tobias-weiss-ai-xr/mykovolt/docs/technical/MykoVolt_Papers.md

# Paper Collection — Fungal Bio-Battery / Mycelium Electronics

> **Stand:** Juni 2026 | **Kuratierte Sammlung** aus den Bereichen Pilz-MFC, Myzel-Elektronik, Laccase-Bioelektrochemie, Yeast-Biofuel-Cells, MycelioTronics, AI-gestützte Forschung und Marktberichte.
>
> Alle Papers nach Relevanz und Themenclustern sortiert. DOIs und Direktlinks wo verfügbar.

---

## 1. KERN: 3D-gedruckte Pilz-Batterie (Empa)

| # | Titel | Autoren | Journal | Jahr | DOI / Link |
|---|---|---|---|---|---|
| 1 | **3D Printed Cellulose-Based Fungal Battery** | C. Reyes, E. Fivaz, Z. Sajó, A. Schneider, G. Siqueira, J. Ribera, A. Poulin, F.W.M.R. Schwarze, G. Nyström | ACS Sustainable Chemistry & Engineering | 2024 | [10.1021/acssuschemeng.4c05494](https://doi.org/10.1021/acssuschemeng.4c05494) |
| 2 | Empa Pressemitteilung: Fungal biobattery | — | empa.ch | 2025 | [empa.ch/web/s604/fungal-biobattery](https://www.empa.ch/web/s604/fungal-biobattery) |
| 3 | News: The battery that eats itself | H. Hall | R&D World | 2025 | [rdworldonline.com/...](https://www.rdworldonline.com/the-battery-that-eats-itself-fungal-power-with-a-built-in-cleanup-crew/) |
| 4 | News: Swiss scientists have taught fungi to generate electricity | — | Euronews | 2025 | [euronews.com/...](https://www.euronews.com/2025/01/11/swiss-scientists-have-taught-fungi-to-generate-electricity-how-do-mushroom-batteries-work) |
| 5 | News: 3D-printed battery made from fungi feeds on sugars | — | New Atlas | 2025 | [newatlas.com/...](https://newatlas.com/energy/3d-printed-battery-fungi-sugars-empa/) |
| 6 | News: 3D-printed fungi batteries: A path to a biodegradable tech future? | — | Anadolu Ajansı | 2025 | [aa.com.tr/...](https://www.aa.com.tr/en/science-technology/3d-printed-fungi-batteries-a-path-to-a-biodegradable-tech-future/3463854) |

**Key Facts (Reyes 2024):**
- Erstmalige Kombination von Hefe (Anode) + Weißfäulepilz (Kathode) in 3D-gedruckter MFC
- Drucktinte: Cellulose-Nanokristalle + Nanofibrillen + Carbon Black + Graphitflocken
- Leistung: 12,5 µW/cm², 300–600 mV für mehrere Tage
- 4 Zellen parallel → Sensor-Betrieb für 65 h
- Vollständig biologisch abbaubar (Cellulose-Membran, Bienenwachs-Gehäuse)

---

## 2. REVIEWS & ÜBERSICHTSARBEITEN

| # | Titel | Autoren | Journal | Jahr | DOI / Link |
|---|---|---|---|---|---|
| 7 | **Fungi-Based Microbial Fuel Cells** | A. Sekrecka-Belniak, R. Toczyłowska-Mamińska | Energies (MDPI) | 2018 | [10.3390/en11102827](https://doi.org/10.3390/en11102827) |
| 8 | **Harnessing fungal bio-electricity: a promising path to a cleaner environment** | A. Umar et al. | Frontiers in Microbiology | 2024 | [10.3389/fmicb.2023.1291904](https://www.frontiersin.org/journals/microbiology/articles/10.3389/fmicb.2023.1291904/full) |
| 9 | **Bioelectricity harvesting from microorganism: review of recent advancements in utilizing the bioelectric properties of fungi for powering small-scale robotic systems** | — | Frontiers in Fungal Biology | 2026 | [10.3389/ffunb.2025.1739847](https://www.frontiersin.org/journals/fungal-biology/articles/10.3389/ffunb.2025.1739847/full) |
| 10 | **Fungal fuel cells: an environmentally friendly approach to addressing heavy metal pollution and electricity production** | — | Frontiers in Microbiology | 2026 | [10.3389/fmicb.2026.1825368](https://www.frontiersin.org/journals/microbiology/articles/10.3389/fmicb.2026.1825368/full) |
| 11 | **The Role of Fungal Fuel Cells in Energy Production and the Removal of Pollutants from Wastewater** | — | Catalysts (MDPI) | 2023 | [10.3390/catal13040687](https://doi.org/10.3390/catal13040687) |
| 12 | **Fungal-mediated electrochemical system: Prospects, applications and challenges** | — | PMC / ScienceDirect | 2021 | [pmc.ncbi.nlm.nih.gov/articles/PMC8610361](https://pmc.ncbi.nlm.nih.gov/articles/PMC8610361/) |
| 13 | **Fungal-mediated microbial electrochemical system: Exciting development, possible application and certain challenges** | — | ResearchGate | 2021 | [researchgate.net/...](https://www.researchgate.net/publication/351976135_Fungal-mediated_microbial_electrochemical_system_Exciting_development_possible_application_and_certain_challenges) |
| 14 | **Recent trends in upgrading the performance of yeast as electrode biocatalyst in microbial fuel cells** | — | Chemosphere | 2021 | [10.1016/j.chemosphere.2021.131330](https://www.sciencedirect.com/science/article/abs/pii/S0045653521018555) |
| 15 | **Microbial Biofuel Cells: Fundamental Principles, Development and Recent Obstacles** | — | Biosensors (MDPI) | 2023 | [pmc.ncbi.nlm.nih.gov/articles/PMC9954062](https://pmc.ncbi.nlm.nih.gov/articles/PMC9954062/) |
| 16 | **New horizons in microbial fuel cell technology: applications, challenges, and prospects** | — | Biotechnol. Biofuels Bioprod. | 2025 | [10.1186/s13068-025-02649-y](https://link.springer.com/article/10.1186/s13068-025-02649-y) |
| 17 | **Harnessing the power of microbial fuel cells as pioneering green technology** | — | Bioprocess Biosyst. Eng. | 2025 | [10.1007/s00449-024-03115-z](https://link.springer.com/article/10.1007/s00449-024-03115-z) |
| 18 | **A Review of Recent Advances in Microbial Fuel Cells: Preparation, Operation, and Application** | — | BioTech (MDPI) | 2022 | [pmc.ncbi.nlm.nih.gov/articles/PMC9589990](https://pmc.ncbi.nlm.nih.gov/articles/PMC9589990/) |

---

## 3. HÖCHSTLEISTUNGSSTUDIEN

### 3.1 Phanerochaete chrysosporium (Weißfäule — 1,9 W/m²)

| # | Titel | Leistung | Journal | Jahr | DOI / Link |
|---|---|---|---|---|---|
| 19 | **Self-Sustaining Bioelectrochemical Cell from Fungal Degradation of Lignin-Rich Agrowaste** | **1,9 W/m²** (3,1 A/m²), **1056 mAh**, 44 Tage @ 1 mA, OCV 1,2 V | Energies (MDPI) | 2021 | [10.3390/en14082098](https://doi.org/10.3390/en14082098) |
| 20 | Conversion of lignocellulosic biomass: Production of bioethanol and bioelectricity using wheat straw hydrolysate | 65,09 mW/m² | Bioresour. Technol. | 2023 | [pmc.ncbi.nlm.nih.gov/articles/PMC9873701](https://pmc.ncbi.nlm.nih.gov/articles/PMC9873701/) |

**⭐ Wichtigste Einzelstudie:** Sukri et al. 2021 — mit *P. chrysosporium* wurde die höchste je gemessene Leistung einer Pilz-MFC erreicht (1,9 W/m²). Zink/Luft-Zelle, membranlos, 44 Tage stabil.

### 3.2 Trametes versicolor

| # | Titel | Leistung | Journal | Jahr | DOI / Link |
|---|---|---|---|---|---|
| 21 | A white-rot fungus is used as a biocathode to improve electricity production of an MFC | 320 ± 30 mW/m³ (laccase: 480 mW/m³) | Applied Energy | 2012 | — |
| 22 | In situ Trametes versicolor laccase biocathode performance assessment in dual-chamber MFCs | 42,8 mA/m² (2,1× Kontrolle) | Bioenergy Research | 2023 | [10.1007/s12155-023-10594-7](https://doi.org/10.1007/s12155-023-10594-7) |
| 23 | Hybrid microbial–enzymatic fuel cell cathode overcomes enzyme inactivation limits | Self-regenerierende Kathode | Catalysts (MDPI) | 2021 | [mdpi-res.com/.../catalysts-11-00242.pdf](https://mdpi-res.com/d_attachment/catalysts/catalysts-11-00242/article_deploy/catalysts-11-00242-v3.pdf) |
| 24 | Decolorization of azo dye and generation of electricity by MFC with laccase-producing white-rot fungus on cathode | 276,9 mW/m² | Applied Energy | 2017 | — |

### 3.3 Ganoderma lucidum & Ganoderma gibbosum

| # | Titel | Leistung | Journal | Jahr | DOI / Link |
|---|---|---|---|---|---|
| 25 | **Electricity generation and oxidoreductase potential during dye discoloration by laccase-producing Ganoderma gibbosum in fungal fuel cell** | 810 mV OCV, 14,18 mW/m², 35 mA/m² | Microb. Cell Fact. | 2023 | [10.1186/s12934-023-02258-0](https://microbialcellfactories.biomedcentral.com/articles/10.1186/s12934-023-02258-0) |
| 26 | Ganoderma lucidum BCRC 36123 als Biokathode | 207 mW/m² | diverse | — | — |

### 3.4 Pleurotus spp. (Austernpilze)

| # | Titel | Leistung | Journal | Jahr | DOI / Link |
|---|---|---|---|---|---|
| 27 | Improved Performance of a Novel-Model Laccase-based MFC (Pleurotus pulmonarius) | **940 mV** OCV, 13,22 mW/m², 97 mA/m² | PJOES | 2023 | [pjoes.com/pdf-147196-78069](https://www.pjoes.com/pdf-147196-78069) |
| 28 | Reducing Plastic Waste and Generating Bioelectricity Simultaneously — Pleurotus ostreatus | 86,3 mW/cm² (!), 0,427 V | Sustainability (MDPI) | 2024 | [doi.org/10.3390/su16187909](https://www.mdpi.com/2071-1050/16/18/7909) |
| 29 | MIND Device: Mycoponically Integrated Network Device — Pleurotus ostreatus | >11 Monate stabiles Myzel-Netzwerk | arXiv | 2026 | [arxiv.org/html/2604.22947](https://arxiv.org/html/2604.22947) |
| 30 | Selective natural induction of laccases in Pleurotus sajor-caju for biofuel cell cathode | −148 µA/cm² bei pH 5; −102 µA/cm² bei pH 7 | Bioresour. Technol. | 2016 | — |

### 3.5 Aspergillus, Paecilomyces, Trichoderma (Plastikabbau)

| # | Titel | Pilz | Leistung | Journal | Jahr | DOI / Link |
|---|---|---|---|---|---|---|
| 31 | Performance of the Dual-Chamber Fungal Fuel Cell in Treating Tannery Wastewater | *A. niger* | 0,814 V, COD 77,9 % | Appl. Sci. | 2023 | [10.3390/app131910710](https://www.mdpi.com/2076-3417/13/19/10710) |
| 32 | Sustainable Use of Aspergillus sp. to Generate Electricity and Reduce Plastic | *Aspergillus* sp. | 0,572 V, 0,124 mW/cm², COD 73,8 % | Sustainability | 2024 | [10.3390/su16177413](https://www.mdpi.com/2071-1050/16/17/7413) |
| 33 | Electricity Generation and Plastic Waste Reduction Using Paecilomyces | *Paecilomyces* | 0,575 V, 0,062 mW/cm², COD 85,5 % | Sustainability | 2024 | [10.3390/su162411137](https://www.mdpi.com/2071-1050/16/24/11137) |
| 34 | Potential Use of Trichoderma sp. as a Plastic-Reducing Agent and Electricity Generator | *Trichoderma* sp. | 0,479 V, 68,1 mW/cm² | Processes (MDPI) | 2024 | [10.3390/pr12122904](https://www.mdpi.com/2227-9717/12/12/2904) |
| 35 | Enhancing Electricity Generation Using Fungal Laccase-Based MFC (*Monodictys castaneae*) | *M. castaneae* | 0,807 V mit Agro-Abfall; Phenolabbau 99,7 % | JMBFS | 2024 | [10.55251/jmbfs.9703](https://office2.jmbfs.org/index.php/JMBFS/article/view/9703) |
| 36 | Fungi-based microbial fuel cells: A sustainable solution for filter mud | *M. pseudolusitanicus* | 47,3 mW/m², COD 67 % | Env. Cons. J. | 2026 | [journal.environcj.in/.../3517](https://journal.environcj.in/index.php/ecj/article/view/3517) |

### 3.6 Xeno-Fungusphere (Agrar-Anwendung)

| # | Titel | System | Leistung | Journal | Jahr | DOI / Link |
|---|---|---|---|---|---|---|
| 37 | **Xeno-Fungusphere: Fungal-Enhanced MFCs for Agricultural Remediation** | *P. chrysosporium* + *T. versicolor* + Biofeld | **9,3 µW/cm²**, Herbizid-Abbau 97,9 % | Agriculture (MDPI) | 2025 | [10.3390/agriculture15061392](https://www.mdpi.com/2073-4395/15/6/1392) |

---

## 4. MYCELIOTRONICS — Myzel als Batterie-Separator & Gehäuse

| # | Titel | Autoren | Journal | Jahr | DOI / Link |
|---|---|---|---|---|---|
| 38 | **MycelioTronics: Fungal mycelium skin for sustainable electronics** | — | **Science Advances** | 2022 | [10.1126/sciadv.add7118](https://www.science.org/doi/10.1126/sciadv.add7118) |
| 39 | MycelioTronics: Fungal mycelium skin (JKU-Volltext) | Kaltenbrunner et al. | epub.jku.at | 2022 | [epub.jku.at/.../9001930](https://epub.jku.at/obvulioa/download/pdf/9001930) |
| 40 | MycelioTronics: Fungal mycelium skin (PMC) | — | PMC | 2022 | [pmc.ncbi.nlm.nih.gov/articles/PMC9651864](https://pmc.ncbi.nlm.nih.gov/articles/PMC9651864/) |
| 41 | Physics World: Mushroom-based substrates create flexible and sustainable electronics | — | Physics World | 2022 | [physicsworld.com/...](https://physicsworld.com/a/mushroom-based-substrates-create-flexible-and-sustainable-electronics/) |
| 42 | Are fungal mycelium skin-derived MycelioTronics an environmentally friendly substitute? | — | News-Medical | 2022 | [news-medical.net/...](https://www.news-medical.net/news/20221115/Are-fungal-mycelium-skin-derived-MycelioTronics-an-environmentally-friendly-substitute-for-electronics.aspx) |

**Key Facts (MycelioTronics):**
- *Ganoderma lucidum*-Myzel als flexibles Substrat + Separator für Zink-Kohle-Batterien
- Kapazität: **3,8 mAh/cm²**
- Leiterbahn-Leitfähigkeit: 9,75 × 10⁴ S/cm (PVD Gold/Kupfer)
- >2000 Biegezyklen standgehalten
- Bluetooth Low Energy (13,5 mA Betrieb) mit 2 Zellen in Serie betrieben
- 93 % Masseverlust im Kompost nach 11 Tagen

---

## 5. HEFE-BASIERTE BIO-BATTERIEN (Saccharomyces cerevisiae)

| # | Titel | Leistung | Journal | Jahr | DOI / Link |
|---|---|---|---|---|---|
| 43 | **Yeast bio-batteries** (Crespilho) | **450 mV**, rechargeable, PET-Elektroden | RSC Sustainable Energy | 2024 | [pubs.rsc.org/.../d4se00903g](https://pubs.rsc.org/en/content/articlepdf/2024/se/d4se00903g) |
| 44 | Yeast biofilm synapse: intra-kingdom pathway to high-density current | — | J. Mater. Chem. B | 2025 | [10.1039/D4TB02472A](https://pubs.rsc.org/en/content/articlelanding/2025/tb/d4tb02472a) |
| 45 | Effect of Gold Nanoparticles in MFCs Based on Polypyrrole-Modified S. cerevisiae | **150 mW/m²** (PBS), **179,2 mW/m²** (Abwasser) | Biosensors (MDPI) | 2024 | [10.3390/bios14120572](https://www.mdpi.com/2079-6374/14/12/572) |
| 46 | Enhancing Electron Transfer Efficiency in MFCs Through Gold Nanoparticle Modification of S. cerevisiae | 22,8 mW/m² (4× über unmodifiziert) | PMC | 2025 | [pmc.ncbi.nlm.nih.gov/articles/PMC12388726](https://pmc.ncbi.nlm.nih.gov/articles/PMC12388726/) |
| 47 | Application of response surface methodology for bioenergy generation in yeast-based MFC | 219,3 mW/m², 70 % TOC | RSC Advances | 2024 | [10.1039/D4RA05380J](https://pubs.rsc.org/en/content/articlehtml/2024/ra/d4ra05380j) |
| 48 | Microbial Biofuel Cell: Harnessing Bioelectricity from Fisheries Wastewater Using S. cerevisiae | — | BITYED | 2025 | [dergipark.org.tr/.../1751259](https://dergipark.org.tr/en/pub/bityed/article/1751259) |
| 49 | Bioelectrochemical systems and engineered living materials (BES + ELM Tutorial) | — | Sustainable Energy Fuels | 2025 | [10.1039/D5SE00344J](https://pubs.rsc.org/en/content/articlelanding/2025/se/d5se00344j) |

---

## 6. LACCASE & ENZYM-ENGINEERING

| # | Titel | Fokus | Journal | Jahr | DOI / Link |
|---|---|---|---|---|---|
| 50 | **Discovery of alkaline laccases from basidiomycete fungi through ML-based approach** | **ML** zur Vorhersage von pH-Optima | Biotechnol. Biofuels Bioprod. | 2024 | [10.1186/s13068-024-02566-6](https://link.springer.com/article/10.1186/s13068-024-02566-6) |
| 51 | **Designed High-Redox Potential Laccases Exhibit High Functional Diversity** | PROSS + FuncLib Enzym-Design | ACS Catalysis | 2022 | PMID: [36366766](https://pubmed.ncbi.nlm.nih.gov/36366766/) |
| 52 | Engineering of a fungal laccase to develop a robust, versatile and highly-expressed biocatalyst | Directed Evolution + C-Terminal-Tail | Green Chemistry | 2019 | [10.1039/C9GC02475A](https://pubs.rsc.org/en/content/articlelanding/2019/gc/c9gc02475a) |
| 53 | Fungal Laccases: Fundamentals, Engineering and Classification Update | Übersicht + Klassifikation | Biomolecules (MDPI) | 2023 | [digital.csic.es/.../biomolecules_aza_2023.pdf](https://digital.csic.es/bitstream/10261/352411/1/biomolecules_aza_2023.pdf) |
| 54 | Fungal Laccases: The Forefront of Enzymes for Sustainability | Übersicht | J. Fungi (MDPI) | 2021 | [10.3390/jof7121048](https://www.mdpi.com/2309-608X/7/12/1048) |
| 55 | Laccase: a multi-purpose biocatalyst at the forefront of biotechnology | Übersicht | Microb. Biotechnol. | 2017 | [10.1111/1751-7915.12422](https://enviromicro-journals.onlinelibrary.wiley.com/doi/10.1111/1751-7915.12422) |
| 56 | An Engineered Laccase from Fomitiporia mediterranea Accelerates Lignocellulose Degradation | CBM-Fusion | Biomolecules (MDPI) | 2024 | [10.3390/biom14030324](https://www.mdpi.com/2218-273X/14/3/324) |
| 57 | Protein Engineering Approaches to Enhance Fungal Laccase Production in S. cerevisiae | Übersicht | Int. J. Mol. Sci. | 2021 | [10.3390/ijms22031157](https://www.mdpi.com/1422-0067/22/3/1157) |
| 58 | Genome-based engineering of ligninolytic enzymes in fungi | CRISPR, directed evolution | Microb. Cell Fact. | 2021 | [10.1186/s12934-021-01510-9](https://microbialcellfactories.biomedcentral.com/articles/10.1186/s12934-021-01510-9) |
| 59 | A novel laccase-catalyzed cathode for microbial fuel cells | Immobilisierte Laccase → ersetzt Pt-Kathode | Chem. Eng. J. | 2010 | — |
| 60 | Encapsulated laccase electrodes for fuel cell cathodes | Verkapselte Laccase | J. Electroanal. Chem. | 2005 | — |
| 61 | Fungal Laccases and their Biotechnological Significances | Übersicht | Curr. Org. Chem. | 2015 | [10.2174/1385272819666150629175237](https://www.benthamdirect.com/content/journals/coc/10.2174/1385272819666150629175237) |
| 62 | Green Energy Generation Using Microbial Laccase Enzyme | Übersicht | — | 2023 | [hrcak.srce.hr/file/455777](https://hrcak.srce.hr/file/455777) |

---

## 7. AI & MACHINE LEARNING (für Batterie-Forschung & Bioink-Optimierung)

| # | Titel | Methode | Journal | Jahr | DOI / Link |
|---|---|---|---|---|---|
| 63 | **Integrated high-throughput robotic platform and active learning for accelerated discovery of optimal electrolyte formulations** | **Active Learning + Robotik** | Nature Comm. | 2024 | [osti.gov/biblio/2471574](https://www.osti.gov/biblio/2471574) |
| 64 | **Expert-Guided LLM Reasoning for Battery Discovery (ChatBattery)** | **LLM-gesteuerte Batteriematerial-Entdeckung** | arXiv | 2025 | [arxiv.org/pdf/2507.16110](https://arxiv.org/pdf/2507.16110) |
| 65 | **Foundation Models Enabling Multi-Scale Battery Materials Discovery** | **Foundation Models für Batterien** | OpenReview | 2025 | [openreview.net/pdf?id=6pjxodugzO](https://openreview.net/pdf?id=6pjxodugzO) |
| 66 | **Autonomous Discovery of Polymer Electrolyte Formulations with Warm-start Batch Bayesian Optimization** | **Bayesian Optimization** | ChemRxiv | 2025 | [10.26434/chemrxiv-2025-2cjbg](https://doi.org/10.26434/chemrxiv-2025-2cjbg) |
| 67 | End-to-End Optimization for Battery Materials by Combining GNNs and RL | GNN + Reinforcement Learning | NREL | 2025 | [docs.nlr.gov/.../90377.pdf](https://docs.nlr.gov/docs/fy25osti/90377.pdf) |
| 68 | Accelerating discovery of solid-state electrolytes: a machine learning approach | Logistic Regression ML für NASICON | PCCP (RSC) | 2025 | [10.1039/D4CP04043K](https://pubs.rsc.org/en/content/articlelanding/2025/cp/d4cp04043k) |
| 69 | Application-oriented design of machine learning paradigms for battery science | Review | npj Comput. Mater. | 2025 | [10.1038/s41524-025-01575-9](https://www.nature.com/articles/s41524-025-01575-9) |
| 70 | Towards Self-Driving Labs for Better Batteries | Bayesian Opt. + self-driving lab | ECS Meeting Abstr. | 2025 | [10.1149/MA2025-01188mtgabs](https://iopscience.iop.org/article/10.1149/MA2025-01188mtgabs) |
| 71 | **Bioink Formulation and ML-Empowered Bioprinting Optimization** | **ML für Drucktinten** | Front. Bioeng. Biotechnol. | 2022 | [10.3389/fbioe.2022.913579](https://www.frontiersin.org/journals/bioengineering-and-biotechnology/articles/10.3389/fbioe.2022.913579/full) |
| 72 | **A Deep Learning Quality Control Loop of the Extrusion-based Bioprinting Process** | **CNN-Feedback-Loop** | PMC | 2022 | [pmc.ncbi.nlm.nih.gov/articles/PMC9668573](https://pmc.ncbi.nlm.nih.gov/articles/PMC9668573/) |
| 73 | **AI-powered printability evaluation framework using Hausdorff distance metrics** | **CNN, R²=0,986** | Biofabrication (IOP) | 2025 | [10.1088/1758-5090/ae288c](https://iopscience.iop.org/article/10.1088/1758-5090/ae288c) |
| 74 | **ML in Predicting Printable Biomaterial Formulations for Direct Ink Writing** | **RF 88,1 % accuracy** | PMC | 2023 | [pmc.ncbi.nlm.nih.gov/articles/PMC10353544](https://pmc.ncbi.nlm.nih.gov/articles/PMC10353544/) |
| 75 | **Prediction of strain engineerings that amplify recombinant protein secretion (MaLPHAS)** | **ML für Strain Engineering** | PMC | 2023 | [pmc.ncbi.nlm.nih.gov/articles/PMC9995161](https://pmc.ncbi.nlm.nih.gov/articles/PMC9995161/) |
| 76 | Machine Learning in Gel-Based Additive Manufacturing | Review | Gels (MDPI) | 2025 | [10.3390/gels11080582](https://www.mdpi.com/2310-2861/11/8/582) |

---

## 8. LCA, NACHHALTIGKEIT & MARKT

| # | Titel | Fokus | Journal | Jahr | DOI / Link |
|---|---|---|---|---|---|
| 77 | **Evaluation of environmental performance of MFCs with LCA and PROMETHEE** | **Ökobilanz MFC** | RSC Environ. Sci. Water | 2024 | [10.1039/d3ew00809f](https://pubs.rsc.org/en/content/articlelanding/2024/ew/d3ew00809f) |
| 78 | **Life cycle assessment of microalgae-assisted MFCs** | **LCA MFC + Algen** | Int. J. Life Cycle Assess. | 2025 | [10.1007/s11367-025-02518-8](https://doi.org/10.1007/s11367-025-02518-8) |
| 79 | Life Cycle Assessment of Lithium-ion Batteries: A Critical Review | Li-Ion LCA Review | Resour. Conserv. Recycl. | 2022 | — |
| 80 | Life cycle assessment of large-scale battery systems (LCA + LCC) | Batterie-LCA | Batteries (MDPI) | 2024 | [discovery.ucl.ac.uk/.../batteries-10-00295.pdf](https://discovery.ucl.ac.uk/id/eprint/10211311/1/batteries-10-00295.pdf) |
| 81 | **Biobatteries Market Size, Share & Trends Report, 2035** | **Markt: $96,1 Mrd. → $230 Mrd.** | Roots Analysis | 2025 | [rootsanalysis.com/biobatteries-market](https://www.rootsanalysis.com/biobatteries-market) |
| 82 | **Bio-based Battery Market Size, Share, Industry Report, 2033** | **Medizintechnik 35 % des Markts** | Grand View Research | 2025 | [grandviewresearch.com/...](https://www.grandviewresearch.com/industry-analysis/bio-based-battery-market-report) |
| 83 | **Bio Based Battery Market in the World / US** | **Sustainability-Premium 30–50 %** | IndexBox | 2026 | [indexbox.io/...](https://www.indexbox.io/store/world-bio-based-battery-market-analysis-forecast-size-trends-and-insights/) |

---

## 9. WEITERE RELEVANTE PUBLIKATIONEN

| # | Titel | Fokus | Journal | Jahr | DOI / Link |
|---|---|---|---|---|---|
| 84 | **Mycoelectronics: Bioprinted Living Fungal Bioelectronics for Artificial Sensation** | Thermo-responsive Myzel-Elektronik | NSF / Nature | 2025 | [par.nsf.gov/biblio/10650372](https://par.nsf.gov/biblio/10650372-mycoelectronics-bioprinted-living-fungal-bioelectronics-artificial-sensation) |
| 85 | **Sustainable memristors from shiitake mycelium for high-frequency bioelectronics** | 5,85 kHz, 90 %, strahlungsresistent | PLOS ONE | 2025 | [10.1371/journal.pone.0328965](https://journals.plos.org/plosone/article/file?id=10.1371%2Fjournal.pone.0328965&type=printable) |
| 86 | **MIND Device: Mycoponically Integrated Network Device** | Pilz-Sensornetzwerk >11 Monate | arXiv | 2026 | [arxiv.org/html/2604.22947](https://arxiv.org/html/2604.22947) |
| 87 | **MyceliClean: Harnessing Fungal Bioelectricity for Off-Grid Water Sterilisation** | Wassersterilisation mit 0,78 V Myzel-Batterie | CSO Ireland | 2026 | [cso.ie/.../18_Myceliclean.pdf](https://www.cso.ie/en/media/csoie/competitionsandawards/johnhooper/2026/18_Myceliclean_Harnessing_Fungal_Bioelectricity_for_Off-Grid_Water_Sterilisation.pdf) |
| 88 | Biofuel Cells Based on Oxidoreductases and Electroactive Nanomaterials | Enzym-BFC | Biosensors (MDPI) | 2025 | [10.3390/bios15040249](https://www.mdpi.com/2079-6374/15/4/249) |
| 89 | Recent Advances in Enzymatic Fuel Cells: Experiments and Modeling | Enzym-BFC Review | Energies (MDPI) | 2010 | [10.3390/en3040803](https://www.mdpi.com/1996-1073/3/4/803) |
| 90 | Recent Advances in Microfluidic Biofuel Cells | µ-BFC Review | Biosensors (MDPI) | 2025 | [10.3390/bios15090627](https://www.mdpi.com/2079-6374/15/9/627) |
| 91 | Bio-electrochemical energy recovery: the role of MFCs in waste utilization | Review | Discov. Biotechnol. | 2025 | [10.1007/s44340-025-00025-y](https://link.springer.com/article/10.1007/s44340-025-00025-y) |
| 92 | Yeast-Based MFCs: Recent trends in upgrading performance | Review | Chemosphere | 2021 | — |

---

## Schnellüberblick: Top 10 Must-Read Papers

| Rang | Paper | Warum |
|---|---|---|
| ⭐ | #1 Reyes 2024 (3D Printed Cellulose-Based Fungal Battery) | **Die Proof-of-Concept-Studie** — Grundlage für das ganze Startup |
| ⭐ | #19 Sukri 2021 (Self-Sustaining Bioelectrochemical Cell, P. chrysosporium) | **Höchste Leistung** (1,9 W/m², 1056 mAh) — das Optimierungsziel |
| ⭐ | #38 MycelioTronics (Sci. Adv. 2022) | **Myzel als Batterie-Gehäuse** — paralleler Ansatz, sehr reif |
| ⭐ | #50 ML Laccase pH Discovery (Biotechnol. Biofuels 2024) | **KI-gestützte Stamm-Selektion** — der IP-Moat |
| ⭐ | #8 Umar 2024 (Harnessing fungal bio-electricity, Frontiers Review) | **Beste Übersicht** — alle Pilz-Typen mit Leistungen tabellarisch |
| ⭐ | #7 Sekrecka-Belniak 2018 (Fungi-Based MFCs, Energies Review) | **Standard-Review** — Referenzwerk |
| ⭐ | #43 Crespilho 2024 (Yeast bio-batteries, RSC) | **Hefe-Batterie** — Alternative zum Empa-Ansatz |
| ⭐ | #19 Sukri 2021 (Self-Sustaining Bioelectrochemical Cell) | Siehe oben — wichtigster Einzelpunktwert |
| ⭐ | #63 Active Learning Electrolytes (Nature Comm. 2024) | **KI für Formulierungsoptimierung** — der Effizienzhebel |
| ⭐ | #81 Roots Analysis (Biobatteries Market 2035) | **Marktzahlen** — $96 Mrd. → $230 Mrd. |

---

## Repo-Information

Teil des Repos: `https://codeberg.org/graphwiz-ai/shrooms`

Stand: Juni 2026. Letzte Aktualisierung dieser Sammlung: 24.06.2026.

Insgesamt: **92 Paper & Berichte** (davon 86 erschlossen via DOI/Link)

**Legende:**
- **Fett** = besondere Relevanz für Startup / Technologie-Kern
- Stern ⭐ = Top 10 Must-Read
- DOI = direkt unter der URL aufrufbar
