tobias-weiss-ai-xr/mykovolt/MykoVolt_Angebot_EMC.md

# Kooperationsangebot MykoVolt — EMC Gießen

---

## 1. Vorstellung

MykoVolt entwickelt 3D-gedruckte Pilz-Brennstoffzellen (MFC) für biologisch abbaubare Bodensensoren. Gründer ist Tobias Weiß (contextual-intelligence.org), Informatiker mit Hintergrund in ML-gestützter Optimierung. Die Technologie nutzt Weißfäulepilze (*Phanerochaete chrysosporium*) als Biokatalysator in Cellulose-Tinte — trocken lagerbar, vor Ort aktivierbar, kompostierbar. Wir befinden uns auf TRL 2: Die simulationsbasierte Optimierung ist abgeschlossen, ein experimenteller Proof-of-Concept steht an. Dafür benötigen wir Zugang zu einem Fachlabor für Pilzkultivierung und elektrochemische Messung.

---

## 2. Was wir vom EMC erwarten

### a) Laborzugang

Zugang zu einem Mykologie- oder Biotechnologie-Labor für Pilzkultivierung und elektrochemische Messung (3–6 Monate).

**Begründung:** Stammkultur, Tintenentwicklung und Potentiostat-Messungen erfordern Fachlabor. Etwaige Kosten für Verbrauchsmaterial (Petrischalen, Malzagar, Tintenrohstoffe, DSMZ-Stämme) belaufen sich auf ca. 5 k€. 3D-Drucker und Potentiostat sind über Uni-Infrastruktur nutzbar.

### b) Mentoring

Begleitung durch Bio- oder Materialwissenschaftler.

**Begründung:** Interdisziplinäre Validierung der Tintenformulierung und Messprotokolle durch fachkundige Dritte erhöht die Qualität und Glaubwürdigkeit der Ergebnisse.

### c) EXIST-Vorbereitung

Unterstützung bei der Vorbereitung des EXIST-Gründungsstipendium-Antrags (Herbst 2026).

**Begründung:** Das EMC verfügt über Erfahrung mit EXIST-Anträgen und kann bei der Businessplan-Erstellung und der Förderfit-Prüfung unterstützen.

### d) Netzwerk

Vermittlung zu relevanten Professuren der JLU Gießen (Biologie, Materialwissenschaft).

**Begründung:** Bachelor- und Masterarbeiten sollen PoC-Aufgaben übernehmen (Myzel-Kultivierung, Tintenformulierung, elektrochemische Charakterisierung).

---

## 3. Was wir bringen

- **Innovationsprojekt:** Pilz-Brennstoffzelle kombiniert mit KI-gestützter Tintenoptimierung — hochgradig sichtbar, publikationsfähig.
- **Publikationspotential:** Data-Driven Tintenoptimierung ist neu in der MFC-Literatur. Gemeinsame Paper mit Uni-Partnern sind möglich.
- **Studierende:** Konkrete Projektthemen für Abschlussarbeiten in Biologie, Materialwissenschaft und Informatik.
- **StartUp-Potential:** EXIST-kompatible Gründungsidee mit klarer Zielanwendung (AgrarTech-Bodensensorik) und definierbarem Marktfenster.

---

## 4. Zeitplan

| Phase | Zeitraum | Inhalt |
|---|---|---|
| Start | Jetzt | Laborzugang klären, DSMZ-Stamm bestellen |
| PoC 1 | Monat 1–3 | Stammkultur, Tintenformulierung, Druck, elektrochemische Messung |
| PoC 2 | Monat 3–5 | Boden-Konkurrenzstest (Ackererde) |
| PoC 3 | Monat 5–9 | Sensor-Kit Prototyp (NFC/LoRa-Integration) |
| Antrag | Herbst 2026 | EXIST-Gründungsstipendium einreichen |

---

## 5. Next Steps

1. Gemeinsame Lab-Besichtigung: Welche Labore am EMC oder über die JLU stehen zur Verfügung?
2. Vorstellung bei relevanten Professuren: Wer könnte als wissenschaftlicher Begleiter infrage kommen?
3. Zeitplan und Rahmenbedingungen abstimmen: Nächster konkreter Schritt (DSMZ-Bestellung, Laboraufnahme).
