tobias-weiss-ai-xr/mykovolt/MykoVolt_LinkedIn_Pitch.md

# LinkedIn Pitch Video — Skript (konservativ)

> **Zielplattform:** LinkedIn (Video-Post oder Company Page)
> **Zieldauer:** 60–75 Sekunden
> **Ton:** Authentisch, konkret, wissenschaftlich präzise. Keine übertriebenen Claims.
> **Format:** Talking-Head mit B-Roll (Pilz-Labor, Sensor im Feld, 3D-Druck)

---

## Skript

### 🎬 SZENE 1 — HOOK (0:00–0:08)

**Visuell:** Nahaufnahme Pilzmyzel auf Petrischale, dann Cut zum Sprecher.

**Sprecher (Kamera):**
> „Ein Pilz, der Strom produziert? Klingt absurd — ist aber gemessene Wissenschaft. Und könnte eine Nische füllen, die keine Lithium-Batterie kann."

---

### 🎬 SZENE 2 — PROBLEM (0:08–0:22)

**Visuell:** Drohnenshot über Maisfeld. Overlay: „Tausende Sensoren – keine Rückholung."

**Sprecher (Voiceover):**
> „Präzisionslandwirtschaft setzt auf tausende verteilte Bodensensoren. Problem: Nach der Ernte sind sie nicht rückholbar. Die Knopfzellen bleiben im Boden. Die EU-Batterieverordnung wird das zum Kostenproblem machen — für Betriebe, die heute noch keine Antwort haben."

---

### 🎬 SZENE 3 — LÖSUNG (0:22–0:42)

**Visuell:** 3D-Drucker druckt Pilz-Elektrode. Zeitraffer Pilzwachstum. Messgerät zeigt 500 mV.

**Sprecher (Kamera):**
> „Unsere Idee: Eine 3D-gedruckte Brennstoffzelle aus Cellulose, angetrieben von lebenden Pilzkulturen. Sie wandelt Zucker in Strom um — Niedrigspannung, aber stabil über Tage. Und nach Gebrauch wird das organische Material von den Pilzen selbst abgebaut. Die Kohlenstoffelektroden bleiben als inertes Material zurück — nicht kompostierbar, aber nicht toxisch. Der Punkt ist: Kein Recycling nötig, weil gar kein giftiger Abfall entsteht."

---

### 🎬 SZENE 4 — AKTUELLER STAND (0:42–0:55)

**Visuell:** Logo Empa, Diagramm Leistungsdichte, Zitat Reyes 2024.

**Sprecher (Voiceover):**
> „Der Proof-of-Concept kommt von der Empa in der Schweiz (Reyes et al. 2024). 300–600 mV, 12 Mikrowatt pro Quadratzentimeter. Genug für einen Temperatursensor. Wir arbeiten daran, leistungsstärkere Pilzstämme in das 3D-Druck-Design zu integrieren — das ist der nächste Schritt. Der breitere Bio-Batterie-Markt wird bis 2035 auf über 200 Milliarden Dollar geschätzt. Aber wir konzentrieren uns erstmal auf eine Nische: Agrarsensoren in regulierten Gebieten."

---

### 🎬 SZENE 5 — CALL TO ACTION (0:55–1:05)

**Visuell:** Sprecher im Labor. Text-Overlay: „Forschungspartner gesucht" + „Pilotkunden ab 2028".

**Sprecher (Kamera):**
> „Wir suchen Forschungspartner aus der Agrarwissenschaft und Sensorhersteller, die eine biologisch abbaubare Alternative für ihre Sensornetzwerke entwickeln wollen. Erste Feldtests sind ab 2028 realistisch. Wer Interesse hat: Schreib mir."

---

### 🎬 SZENE 6 — LOGO (1:05–1:08)

**Visuell:** MykoVolt Logo + „Biologisch abbaubare Energie für die Landwirtschaft."

---

## Änderungen zur Vorversion (konservative Korrekturen)

| Vorher | Nachher | Grund |
|---|---|---|
| „Null Gift" | „Kohlenstoffpartikel inert, nicht toxisch" | Carbon Black ist nicht biologisch abbaubar |
| „Vollständig biologisch abbaubar" | „Organische Komponenten kompostierbar" | Präzise Trennung |
| „Der Markt: $230 Mrd." | „Breiterer Bio-Batterie-Markt… aber wir fokussieren Nische" | Markt ist nicht direkt adressierbar |
| „Piloten ab 2026" | „Erste Feldtests ab 2028" | Realistische TRL-Entwicklung |
| „Millionen Batterien vergiften Böden" | „Tausende Sensoren… Knopfzellen bleiben im Boden" | Keine Panikmache, sachlich |
| „Wissenschaft validiert" | „Proof-of-Concept von Empa" | Validierung bezieht sich auf Baseline, nicht auf MykoVolts modifizierten Ansatz |
| „Wir bringen sie ins Feld" | „Wir arbeiten daran… das ist der nächste Schritt" | Entwicklungspipeline statt Fertigbehauptung |

---

## Hook-Alternativen (A/B-Test)

1. „Ein Pilz, der Strom produziert?" (wissenschaftlich neugierig)
2. „Dein Sensor im Acker — nach der Ernte holt ihn keiner zurück." (Problem-zentriert)
3. „Was, wenn eine Batterie sich selbst kompostiert?" (Visionär)
4. „Lithium-Knopfzellen bleiben für Jahrhunderte im Boden. Muss das sein?" (Provokant)

---

## LinkedIn-Post-Text (konservativ)

> Pilze als Stromquelle — klingt absurd, ist aber gemessene Wissenschaft. 🍄⚡
>
> Wir entwickeln eine 3D-gedruckte Brennstoffzelle aus Cellulose, angetrieben von lebenden Pilzkulturen. Sie wandelt Zucker in Niederspannungsstrom um — für Tage. Die organischen Bestandteile kompostieren nach Gebrauch.
>
> Die Nische: Präzisionslandwirtschaft in ökologisch sensiblen Gebieten, wo tausende Bodensensoren nach der Ernte nicht zurückgeholt werden können. Konventionelle Knopfzellen bleiben — unser Ansatz reduziert den Abfall auf inerten Kohlenstoff.
>
> Der Proof-of-Concept kommt von der Empa (2024). Wir arbeiten an leistungsstärkeren Pilzstämmen für das 3D-Druck-Design. Erste Feldpiloten ab 2028.
>
> 🔍 Wir suchen:
> → Forschungspartner aus Agrarwissenschaft & Sensor-Engineering
> → Pilotbetriebe für Feldtests (ab 2028)
>
> Interesse? Schreib mir.
>
> #Biotech #CircularEconomy #AgrTech #PrecisionFarming #BioBattery #Sustainability

---

## Disclaimer (aktualisiert)

- „MykoVolt" ist Arbeitsname — vor Publikation Markenschutz prüfen (DPMA/EUIPO)
- Empa-IP-Status prüfen — falls Patent(e) bestehen, eigene Entwicklungsroute klar abgrenzen
- **Carbon Black/Graphit** sind nicht biologisch abbaubar → im Pitch klar kommunizieren
- Keine Leistungsversprechen ohne eigene verifizierte Messdaten
- Zeitangabe „Feldpiloten ab 2028" konservativ kalkuliert (TRL 2→7 in 3–4 Jahren)
