tobias-weiss-ai-xr/mykovolt/docs/strategy/one_pager.md

# MykoVolt — One Pager

> **Version:** v2.0 | **Date:** August 2026  
> **Founders:** Tobias (CIO), Marc (BD) + [CTO hiring]  
> **Status:** Pre-seed | **HQ:** Hesse, Germany (+ remote)

---

## 🎯 **What We Do**

MykoVolt develops **biodegradable fungal bio-batteries** that power disposable IoT sensors. Our technology enables **zero-waste sensor networks** that operate underground, in darkness, and **compost away at end-of-life** — eliminating e-waste and compliance headaches.

```
Traditional batteries:  Leave behind toxic waste  →  Must be retrieved
MykoVolt batteries:      Naturally decompose      →  No retrieval needed
```

---

## 🔬 **The Technology**

### How It Works
1. **Fungi consume sugar** → Release electrons through metabolism
2. **Electrons flow** through conductive carbon network → Generate power
3. **Power regional sensors** → Collect data (7-14 days)
4. **Fungi continue growing** → Decompose battery + housing (90 days)

### Key Metrics
| Spec | Current | Target (2027) | Target (2028) |
|---|---|---|---|
| Power density | 12.5 µW/cm² | 50 µW/cm² | 200 µW/cm² |
| Lifetime | 7-14 days | 14-21 days | 30+ days |
| Cost/unit | €5-10 | €0.50 | €0.15 |
| Biodegradability | 90% | 95% | 99% |
| Shelf life | 6 months | 12 months | 18 months |

### IP & Innovation
- ✅ **AI-optimized** strain selection (5-10× faster R&D)
- ✅ **Compression molding** (100× faster than 3D printing)
- ✅ **Rehydration protocol** (multiple use cycles)
- 🟡 **Patent pipeline:** 6 innovations (filed 2026-2027)

---

## 📈 **Market Opportunity**

### The Mandate: EU Battery Regulation
- **2026:** Retrieval required for industrial batteries >5kg
- **2027:** Extended Producer Responsibility for all batteries
- **2028:** Ban on non-replaceable batteries in many devices

**Result:** €68B market **mandated** to switch to biodegradable solutions

### Target Markets (SOM: €68B by 2030)

| Segment | TAM 2030 | Pain Point | MykoVolt Solution |
|---|---|---|---|
| **Agricultural Sensors** | €12.3B | Buried sensors can't be retrieved | Soil moisture tags (€2.50) |
| **Environmental Monitoring** | €8.1B | Protected areas need zero-impact | Wildlife tags, compost monitors |
| **Medical Devices** | €42B | Disposable sensors = Li-ion waste | Wound monitoring patches (€1.20) |
| **Smart Packaging** | €5.6B | Food spoilage = $1T waste | Freshness indicators (€0.80) |
| **Cold Chain** | €14.2B | Temperature logging in transit | Loggers (€1.50) |

### Competitive Landscape
| Company | Tech | vs. MykoVolt |
|---|---|---|
| BeFC | Enzyme paper battery | ⚠️ Shorter lifetime, lower power |
| Bioo | Plant-based battery | ⚠️ Inconsistent performance |
| Bactery | Bacterial MFC | ⚠️ Slower activation (days vs. hours) |
| **MykoVolt** | **Fungal bio-battery** | ✅ **Highest power + fully biodegradable** |

---

## 💰 **Business Model**

### Revenue Streams
1. **Hardware** (60% margin)
   - NFC DevKit: €35 (evaluation platform)
   - End products: €0.80-2.50/unit

2. **Consumables** (75% margin)
   - Fungal pellets: €0.45/unit (refills)

3. **SaaS** (80% margin)
   - Data analytics: €0.05/data-point
   - API access: Subscription

**Revenue mix (2030):** Hardware 40% | Consumables 30% | SaaS 30%

### Financial Projections
| Year | Revenue | Growth | Profitability |
|---|---|---|---|
| 2026 | €175K | — | ❌ (R&D phase) |
| 2027 | €1.875M | 970% | ❌ (Scale-up) |
| 2028 | €13.76M | 635% | ✅ EBITDA: -€2M |
| 2029 | €39.83M | 190% | ✅ EBITDA: €5M |
| 2030 | €91.4M | 129% | ✅ EBITDA: €25M (27%) |

---

## 🚀 **Product Roadmap**

### Phase 0: Validation (2026)
- ✅ **PoC:** Reproduce Empa baseline (12.5 µW/cm²)
- ✅ **DevKit:** NFC evaluation platform
- 🟡 **SOHO Lab:** Pi 5 + Hailo + 3D printers validate 90 papers experimentally
- 🟡 **Open Data:** First fungal bioelectricity monitoring dataset
- 🎯 **Goal:** First 100 DevKits to research labs

### Phase 1: Early Adopters (2027)
- 🟡 **Q2:** Pellet refill production (1K/day)
- 🟡 **Q4:** First agricultural field tests
- 🎯 **Goal:** €1M+ revenue from consumables

### Phase 2: Market Entry (2028)
- 🟡 **Q2:** CE marking certification
- 🟡 **Q4:** First end products (Soil Sensor Tag)
- 🎯 **Goal:** €10M+ revenue

### Phase 3: Scale-Up (2029-2030)
- 🟡 **2029:** FDA clearance for medical
- 🟡 **2029:** Roll-to-roll production (100K/day)
- 🎯 **Goal:** €50M+ revenue by 2030

---

## 🛠️ **Technology Readiness**

### Current Status (TRL 3-4)
- ✅ **Empa baseline** validated in our lab
- ✅ **AI simulation pipeline** operational (20× faster R&D)
- ✅ **Compression molding** prototyped
- ✅ **Research database:** 90+ curated papers

### Next Milestones
- 🟡 **Q4 2026:** First DevKit shipments
- 🟡 **Q2 2027:** 50 µW/cm² achieved
- 🟡 **Q4 2027:** First revenue from consumables
- 🟡 **Q2 2028:** CE marking obtained

---

## 👥 **Team**

| Role | Status | Profile |
|---|---|---|
| **CIO (Tobias)** | ✅ Founder | AI/ML expert, 10+ years simulation |
| **BD (Marc)** | ✅ Founder | Business development, partnerships |
| **CTO** | 🔍 Hiring | Fungal biology/electrochemistry PhD |
| **Advisors** | 🔍 Recruiting | Empa, IoT industry, investors |

**Hiring priorities:**
1. CTO (€80K + equity) — Technical leadership
2. Electrochemist (€60K + equity) — Lab operations
3. Embedded engineer (€65K) — Sensor development

---

## 💸 **Funding**

### Current Status
- **Stage:** Pre-seed
- **Revenue:** €0 (pre-product)
- **Runway:** 12+ months (bootstrapped)

### Funding Needs

| Round | Amount | Use | Timeline | Valuation |
|---|---|-----|---|---|
| **Seed** | €250K | PoC + team | Now | €2.5M |
| **Pre-Series A** | €1.75M | Pilot production | Q1 2027 | €18M |
| **Series A** | €10M | Scale manufacturing | 2028 | €110M |
| **Series B** | €30M | Roll-to-roll + medical | 2029 | €280M |

### Investor Returns
- **Series A:** Target 10x return in 5 years
- **Series B:** Target 8x return in 3 years
- **Exit strategy:** Strategic acquisition (2030+)

---

## 🌍 **Impact**

### Environmental
- **40 tons** e-waste avoided/year (10M sensors)
- **100% biodegradable** vs. <5% Li-ion recycling
- **Zero heavy metals** → No soil/water contamination

### Economic
- **30-50% cost savings** for customers
- **New markets** enabled (protected areas)
- **EU compliance** built-in

### Social
- Enables **sustainable agriculture**
- Supports **circular economy**
- Advances **bio-electronics** field

---

## 🎯 **Why Now?**

1. **Technology:** Empa breakthrough (2024) + 90 new papers curated
2. **Regulation:** EU Battery Regulation mandates change (2026-2028)
3. **Market:** IoT sensor growth (30% CAGR) + sustainability demand
4. **Team:** Founders with AI + business expertise, hiring CTO
5. **Competition:** No direct competitors with biodegradable + scalable solution

**The window is open — and closing fast.**

---

## 📞 **Contact**

**Founders:**
- Tobias: tobias.weiss.ai.xr@gmail.com | [LinkedIn](linkedin.com/company/mykovolt)
- Marc: [Email to be added]

**Legal:**
- Company: MykoVolt GmbH (in formation)
- HQ: Hesse, Germany
- IP: 6 patents pending (2026-2027)

**Resources:**
- Website: [mykovolt.com](https://mykovolt.com) (coming soon)
- GitHub: [github.com/tobias-weiss-ai-xr/mykovolt](https://github.com/tobias-weiss-ai-xr/mykovolt)
- Research: [github.com/tobias-weiss-ai-xr/mykovolt/research](https://github.com/tobias-weiss-ai-xr/mykovolt/blob/main/research/README.md) (90+ papers)
- Docs: [docs.mykovolt.com](https://docs.mykovolt.com) (technical deep dives)

---

## 📌 **Quick Facts**

| Category | Fact |
|---|---|
| **Founded** | 2026 |
| **HQ** | Hesse, Germany |
| **Team size** | 2 founders + hiring |
| **Stage** | Pre-seed |
| **Product** | Biodegradable fungal bio-battery |
| **Market** | €68B (SOM) by 2030 |
| **TAM** | €92B by 2030 |
| **Revenue 2026** | €175K (projected) |
| **Revenue 2030** | €91.4M (projected) |
| **Funding needed** | €250K (Seed) |
| **Valuation (Seed)** | €2.5M |
| **Patents** | 6 pending |
| **Research papers** | 90+ curated |
| **Key innovation** | AI-optimized fungal bio-battery |
| **Biggest moat** | First CE-marked biodegradable battery |

---

*"Power for one use. Zero waste forever."*
