tobias-weiss-ai-xr/mykovolt/docs/outreach/masters_students_recruitment.md

# Master's Thesis Recruitment Post

---

## 🎓 Master's Thesis Opportunities @ MykoVolt

**Build the First Functional Fungal Bio-Battery**

MykoVolt is recruiting **3-4 Master's thesis students** (Q4 2026 / Q1 2027 start) to build the world's first biodegradable fungal bio-battery for IoT sensors.

**Your thesis = First functional prototype** 🍄⚡

---

## Open Topics

### 🔴 CRITICAL PATH (Priority Topics)

#### WP2.1: Compression-Molded Fungal MFC Pellets
**Degree:** M.Sc. Materials Science / Chemical Engineering / Biotechnology
**Start:** Q4 2026 / Q1 2027
**Duration:** 6 months
**Location:** Hesse, Germany (lab work required)

**Task:**
- Develop compression molding process for fungal MFC pellets
- Optimize cellulose-carbon matrix formulation
- Characterize electrochemical performance
- Iterate toward 50-100 µW/cm² target

**Skills:** Materials processing, electrochemistry, DOE

---

#### WP3.1: Ultra-Low-Power MCU Firmware
**Degree:** M.Sc. Electrical Engineering / Embedded Systems / Computer Engineering
**Start:** Q4 2026 / Q1 2027
**Duration:** 6 months
**Location:** Remote possible (some lab visits)

**Task:**
- Develop STM32L0 firmware for soil sensor node
- Implement deep sleep (0.4 µA target) + periodic wake
- Integrate capacitive sensor + ADC + FRAM storage
- Optimize energy budget (~40 mJ/day)

**Skills:** C/C++, STM32, ultra-low-power design, sensors

---

### 🟡 HIGH PRIORITY

#### WP1.1: High-Performance Fungal Strains
**Degree:** M.Sc. Biotechnology / Microbiology / Mycology
**Start:** Q4 2026 / Q1 2027
**Duration:** 6 months
**Location:** Hesse, Germany (lab work required)

**Task:**
- Screen fungal strains (Trametes, Phanerochaete, etc.)
- Reproduce Empa baseline (12.5 µW/cm²)
- Optimize co-culture with yeast (S. cerevisiae)
- Characterize laccase enzyme activity

**Skills:** Microbial cultivation, aseptic technique, enzymology

---

#### WP2.2: Biodegradable Casing Materials
**Degree:** M.Sc. Materials Science / Polymer Engineering
**Start:** Q4 2026 / Q1 2027
**Duration:** 6 months
**Location:** Hesse, Germany (lab work required)

**Task:**
- Develop IP67 compostable casing (1.5 mm wall)
- Test biodegradation (EN 13432 / OK Compost)
- Balance mechanical strength vs. decomposition rate
- Target: 30-90 days composting

**Skills:** Polymer science, materials testing, biodegradation

---

### 🟢 ADDITIONAL TOPICS

#### WP3.2: Boost Converter Optimization
**Degree:** M.Sc. Electrical Engineering / Power Electronics
**Start:** Q4 2026 / Q1 2027
**Duration:** 6 months

**Task:** Optimize DC-DC boost (0.45V → 3.3V) for ultra-low input power

---

#### WP4.1: Soil Dielectric Sensor Calibration
**Degree:** M.Sc. Environmental Engineering / Geoscience
**Start:** Q4 2026 / Q1 2027
**Duration:** 6 months

**Task:** Calibrate capacitive sensor across soil types (sand, loam, clay)

---

#### WP5.1: Life Cycle Assessment (LCA)
**Degree:** M.Sc. Environmental Science / Sustainability
**Start:** Q4 2026 / Q1 2027
**Duration:** 6 months

**Task:** Compare GWP of fungal battery vs. Li-ion (cradle-to-grave)

---

#### WP1.2: Electron Transport Enhancement
**Degree:** M.Sc. Biochemistry / Synthetic Biology
**Start:** Q4 2026 / Q1 2027
**Duration:** 6 months

**Task:** Test redox mediators (ABTS, methylene blue) for power boost

---

#### WP2.3: 3D-Printed Electrode Architectures
**Degree:** M.Sc. Mechanical Engineering / Additive Manufacturing
**Start:** Q4 2026 / Q1 2027
**Duration:** 6 months

**Task:** Design/print optimized electrode geometries (air channels, surface area)

---

#### WP5.2: Field Deployment Strategy
**Degree:** M.Sc. Agricultural Science / Environmental Management
**Start:** Q4 2026 / Q1 2027
**Duration:** 6 months

**Task:** Design pilot deployment protocols (agriculture, forestry, waste)

---

## What You Get

✅ **Real-world impact:** Your thesis builds the first functional prototype
✅ **Publications:** Peer-reviewed paper (first author)
✅ **IP experience:** Named inventor on patents
✅ **Funding:** €500-1000/month stipend (grant-dependent or university-funded)
✅ **Career launchpad:** Deep tech startup experience, network, references
✅ **Supervision:** Co-founder (CTO) + university professor
✅ **Equipment:** Access to lab facilities, potentiostat, 3D printers

---

## Requirements

- Enrolled in M.Sc. program (or completing B.Sc. with direct M.Sc. entry)
- Relevant background (see topic-specific skills above)
- Self-motivated, comfortable in startup environment
- Good English (German is a plus, not required)
- Available for 6 months (full-time thesis work)

---

## How to Apply

**📧 Send to:** tobias.weiss.ai.xr@gmail.com

**Include:**
1. CV + current transcript (GPA)
2. Which topic(s) interest you (rank 1-3 choices)
3. Your university + expected graduation date
4. Relevant skills (lab work, programming, electronics, etc.)
5. Why MykoVolt? (2-3 sentences)

**Process:**
1. Email application → 2. Video call (30 min) → 3. Thesis proposal → 4. Start date

**Timeline:**
- **Q3 2026:** Applications open
- **Q4 2026:** Interviews, thesis proposal
- **Q1 2027:** Thesis begins (prototype build)

---

## FAQ

**Q: Where is the lab located?**
A: Hesse, Germany (Frankfurt/Rhein-Main area). Exact location depends on university partnership (JLU Gießen, TU Darmstadt, or Marburg).

**Q: Is this paid?**
A: Yes, €500-1000/month stipend if grant-funded (Hessen Ideen, EXIST). Otherwise, university-funded positions may be available.

**Q: Can I work remotely?**
A: Lab-based topics (WP1, WP2) require on-site presence. Electronics/software topics (WP3) can be partially remote.

**Q: Who supervises the thesis?**
A: Joint supervision: MykoVolt co-founder (CTO) + university professor.

**Q: Who owns the IP?**
A: MykoVolt retains IP rights; you are named inventor on patents and first author on publications.

**Q: Can this lead to a job?**
A: Yes! Top performers may be offered PhD positions or full-time roles as we scale.

---

## Learn More

🔗 **GitHub:** github.com/tobias-weiss-ai-xr/mykovolt
📄 **Full topic descriptions:** See `docs/outreach/masters_thesis_topics.md` in repo
📧 **Questions?** tobias.weiss.ai.xr@gmail.com

---

**Share this with:** M.Sc. students in Biotechnology, Materials Science, Electrical Engineering, Environmental Science, or related fields.

#MastersThesis #Thesis #Research #Biotechnology #MaterialsScience #ElectricalEngineering #ClimateTech #DeepTech #Sustainability #Bioeconomy #IoT #GreenTech #Students #Hiring #Germany #Hesse
