tobias-weiss-ai-xr/mykovolt/docs/strategy/pitch_deck_outline.md

# MykoVolt Pitch Deck Outline

> **Version:** v2.0 | **Duration:** 12-15 slides | **Style:** Problem-Solution-Impact
> **Audience:** Investors, grants, strategic partners

---

## 🎬 **Slide 1: Title - The Battery That Disappears**

**Headline:**
> MykoVolt: Biodegradable Fungal Bio-Batteries  
> Powering the First Truly Disposable IoT

**Subtitle:**
> 100% compostable | EU-compliant | Zero e-waste

**Visual:**
- Hero image: Mycelium network with sparks (artistic)
- Tagline: "Power for one use. Zero waste forever."

**Speaker notes:**
- Hook: "What if your battery could plant itself?"  
- MykoVolt = Mycology (fungi) + Volt (electricity)
- Based on 90+ peer-reviewed papers + Empa Swiss research

---

## 📉 **Slide 2: The Problem - The Hidden Cost of IoT**

**Headline:** The IoT Wasteland

**Data points:**
- ✓ 30B+ IoT devices deployed by 2030
- ✓ 50% fail within 18 months (battery issues)
- ✓ **Zero** biodegradable battery solutions exist
- ✓ **250 tons** of sensor batteries buried annually (agriculture alone)

**Visual:**
- Image: Landfill with batteries vs. clean field with sensors
- Timeline: Battery lifetime vs. sensor lifetime mismatch

**Speaker notes:**
- EU Battery Regulation 2026: Retrieval required for buried sensors
- Current solutions: Solar (intermittent), Li-ion (retrieval needed), RF (short range)
- Gap: No solution for **buried, long-term, disposable** sensors

---

## 🔬 **Slide 3: The Science - Nature's Power Plant**

**Headline:** Fungi That Generate Electricity

**How it works:**
```
Sugar + O₂ → Fungal metabolism → e⁻ itinerant → Carbon electrode → Power
         ↓
     CO₂ + H₂O  (biodegradation)
```

**Performance:**
- ✓ 50-200 µW/cm² (enough for most sensors)
- ✓ 7-14 days continuous operation
- ✓ 6+ months shelf life (dry storage)
- ✓ 90% biodegradation in <90 days

**Visual:**
- Diagram: Cross-section of fungal MFC
- Comparison: MykoVolt vs. Li-ion vs. Solar

**Speaker notes:**
- Based on Empa (Swiss Federal Labs) research + 15 new papers we curated
- Uses **Trametes** (laccase-producing) + **Saccharomyces** (electron-donating)
- No heavy metals → Exempt from EU battery regulations

---

## 💡 **Slide 4: The Solution - Drop, Monitor, Forget**

**Headline:** The First Battery that Plants Itself

**Product demo:**
```
1️⃣ DROP: Deploy sensor in soil
2️⃣ MONITOR: 7-14 days of data collection
3️⃣ FORGET: Battery + housing biodegrade naturally
```

**Key benefits:**
- ✅ **No retrieval** required
- ✅ **No e-waste**
- ✅ **EU-compliant** by design
- ✅ **Lower TCO** than Li-ion (no retrieval costs)

**Visual:**
- Animation: Sensor deployment → data collection → biodegradation
- Side-by-side: Traditional sensor (retrieval needed) vs. MykoVolt (disappears)

---

## 🎯 **Slide 5: Market Opportunity - The Mandate**

**Headline:** €92B Market Being Forced to Change

**Regulatory catalyst:**
- EU Battery Regulation (2026): Retrieval required for industrial batteries
- Extended Producer Responsibility (2027): All batteries
- Non-replaceable battery ban (2028): Many applications impacted

**Market segmentation:**
| Segment | TAM 2030 | MykoVolt Fit |
|---|---|---|
| Agriculture | €12.3B | ⭐⭐⭐⭐⭐ |
| Environmental | €8.1B | ⭐⭐⭐⭐⭐ |
| Medical | €42B | ⭐⭐⭐⭐⭐ |
| Smart Packaging | €5.6B | ⭐⭐⭐⭐ |
| **Total SOM** | **€68B** | |

**Visual:**
- Bar chart: Market size by segment
- Map: Global regulatory pressure

---

## 🏆 **Slide 6: Competitive Advantage - Why We Win**

**Headline:** 4 Defensible Moats

**1. Technical Moat**
- AI-optimized strain selection
- 5-10× faster R&D than competitors
- Patent pipeline: 6 innovations filed

**2. Manufacturing Moat**  
- Compression molding (100x faster than 3D print)
- Pharma-grade GMP compliant
- €0.15/unit at scale

**3. Regulatory Moat**
- First biodegradable battery with CE mark (2028)
- First FDA-cleared bio-battery (2029)
- 12-18 month first-mover advantage

**4. Data Moat**
- Millions of sensor data points
- Proprietary AI models for anomaly detection
- Recurring revenue from analytics (80% margins)

**Visual:**
- Competitor comparison table (BeFC, Bioo, etc.)
- Moat diagram with defensive walls

---

## 📈 **Slide 7: Product Roadmap - From Lab to Market**

**Timeline:**

```
2026 (Seed)          2027 (Pre-Series A)     2028 (Series A)
━━━━━━━━━━━━━    ━━━━━━━━━━━━       ━━━━━━━━━━━━
PoC            NFC DevKit      Soil Tag        Smart Package
50 µW/cm²  →   €35/unit   →   €2.50/unit  →   €0.80/unit

2029 (Series B)       2030 (Series C+)
━━━━━━━━━━━        ━━━━━━━━━━━
Medical Patch    Mass Production
€1.20/unit →    €0.15/unit
```

**Revenue trajectory:**
- 2026: €175K (DevKits)
- 2027: €1.875M (DevKits + refills)  
- 2028: €13.76M (First products)
- 2029: €39.83M (Scale-up)
- 2030: €91.4M (Mass market)

**Visual:**
- Revenue hockey stick chart
- Product images for each phase

---

## 💰 **Slide 8: Business Model - Razor & Blades 2.0**

**Headline:** Recurring Revenue from Day 1

**Revenue streams:**

1. **Hardware** (60% margins)
   - NFC DevKit: €35 (once)
   - Fungal Pellets: €0.45 (recurring)
   
2. **End Products** (50% margins)
   - Soil Sensor Tag: €2.50
   - Smart Packaging: €0.80
   - Medical Patch: €1.20

3. **SaaS Platform** (80% margins)
   - Data analytics: €0.05/data-point
   - API access: Subscription fees

**Revenue mix (Year 5):**
- Hardware: 40%
- Consumables: 30%
- SaaS: 30%

**Visual:**
- Revenue stream pie chart
- Customer lifetime value calculation

---

## 🛠️ **Slide 9: Technology Validation**

**Headline:** From Empa Research to MykoVolt Product

**Proof points:**
- ✅ **Empa baseline:** 12.5 µW/cm² validated
- ✅ **Strain optimization:** 50 µW/cm² in lab
- ✅ **Rehydration:** 3× cycle validated
- ✅ **Manufacturing:** Compression molding at €0.50/unit
- ✅ **SOHO Lab:** 90 papers being validated experimentally (Pi 5 + Hailo + 3D printers)
- ✅ **Open Data:** First fungal bioelectricity monitoring dataset (standard-setter)

**Next milestones:**
- 🟡 **Q4 2026:** First DevKit shipments
- 🟡 **Q2 2027:** 1K units/day production
- 🟡 **Q4 2027:** First field tests
- 🟡 **Q2 2028:** CE marking certification

**Visual:**
- Lab photos (fungal cultivation, prototype)
- Test data: Power curves, biodegradation timeline

---

## 👥 **Slide 10: Team - The A-Team for Bio-Electronics**

**Headline:** Deep Tech Meets Deep Domain Knowledge

**Founding Team:**

**Tobias Weiss** (CIO)
- AI/ML expert, 10+ years in simulation & optimization
- Built MykoVolt simulation pipeline (50× faster R&D)
- Previous: Research automation for CI

**Marc [Last Name]** (BD)
- Business development, partnerships, grant strategy
- [Background to be added]

**Open: CTO** (Hiring)
- Fungal biology / electrochemistry PhD
- Hands-on lab experience
- Significant equity available

**Advisors:**
- Dr. Carolina Reyes (Empa) - Core IP inventor
- [Industry advisor] - IoT/biotech scale-up
- [Investor advisor] - Deep tech fundraising

**Visual:**
- Team photos + LinkedIn profiles
- Advisor logos (Empa, etc.)

---

## 💸 **Slide 11: Funding Ask - Fueling the Growth**

**Headline:** €1.75M Pre-Series A

**Use of funds:**
- 🟡 **50% Product Development:** PoC → Pilot production
- 🟡 **30% Team:** Hire CTO + 2 engineers
- 🟡 **15% Manufacturing:** Tooling for compression molding
- 🟡 **5% IP:** Patent filings + regulatory

**Milestones with funding:**
- Month 6: First DevKit revenue
- Month 12: 10K units/month production
- Month 18: First industrial pilot
- Month 24: Series A ready (€20M ARR)

**Expected return:**
- Series A: €10M at €110M valuation
- Series B: €30M at €280M valuation
- Exit: €500M+ (2030)

**Visual:**
- Funding allocation pie chart
- Timeline with milestones

---

## 🌍 **Slide 12: Impact - Solving the E-Waste Crisis**

**Headline:** Zero E-Waste by Design

**Environmental impact:**
- 10M sensors/year × 1g = **40 tons e-waste avoided**
- 100% biodegradable vs. <5% recycling rate
- No heavy metals → Zero contamination

**Economic impact:**
- 30-50% cost savings for customers
- New markets enabled (protected areas)
- EU compliance → Mandatory by 2028

**Social impact:**
- Enables sustainable agriculture
- Supports circular economy
- Advances bio-electronics field

**Visual:**
- Before/after: E-waste landfill vs. clean field
- Impact metrics infographic

---

## 🚀 **Slide 13: Traction - Early Momentum**

**Headline:** Validation from Industry & Science

** Letters of Intent:**
- 🟡 [AgriTech Company] - 10K unit pilot (2027)
- 🟡 [Research Lab] - 100 DevKit pre-orders
- 🟡 [Sensor Manufacturer] - Co-development partnership

**Grants & Awards:**
- 🟡 Hessen Ideen (applied) - €50K
- 🟡 EXIST (applied) - €250K
- 🟡 Horizon Europe (planned) - €1.5M

**Research:**
- ✅ 90+ curated papers (largest fungal MFC database)
- ✅ AI simulation pipeline (20× faster R&D)
- ✅ Empa partnership (IP licensing negotiation)

**Visual:**
- Logos of partners/LOIs
- Grant badges

---

## 🎯 **Slide 14: Vision - The Future is Biodegradable**

**Headline:** A World Without Electronic Waste

**2026:** First DevKit shipments  
**2027:** First agricultural pilots  
**2028:** CE marking + Series A  
**2029:** FDA clearance + international expansion  
**2030:** 100M units/year, €50M ARR  
**2035:** **€5B revenue**, #1 in biodegradable power

**The long-term vision:**
> Every disposable electronic device will have MykoVolt inside.  
> Electronic waste will be a relic of the past.

**Visual:**
- Roadmap timeline
- Future vision artwork

---

## 📞 **Slide 15: Call to Action**

**Headline:** Join Us in Building the Future

**For Investors:**
- Seed round: €250K (open)
- Pre-Series A: €1.75M ( launching Q1 2027)
- Expected return: 10x in 5 years

**For Customers:**
- Free DevKit for evaluation (limit 50)
- 50% discount on first 10K units
- Priority pilot program

**For Team Members:**
- CTO: Significant equity, €80K+, remote-friendly
- Engineers: Equity + bonus, €60-70K
- BD/Sales: Commission + equity

**Contact:**
- Email: tobias.weiss.ai.xr@gmail.com
- GitHub: github.com/mykovolt
- LinkedIn: linkedin.com/company/mykovolt

**Visual:**
- Contact info QR codes
- Investors: "Take the leap"
- Partners: "Shape the future"
- Team: "Build with us"

---

## 🎙️ **Speaker Notes: Key Messages**

### Opening Hook (Slide 1):
> "What if I told you the answer to e-waste is growing in your garden? Fungi that eat sugar and generate electricity. It sounds like science fiction, but it's peer-reviewed science from the Swiss Federal Labs. We've curated 90+ papers, and now we're turning it into a business."

### The Problem (Slide 2):
> "Today, deploying soil sensors means either: Using solar panels that don't work underground, Li-ion batteries that must be retrieved, or accepting that 50% will fail prematurely. The EU has had enough — starting in 2026, they're mandating retrieval of industrial batteries. But what if you could just... leave them?"

### The Science (Slide 3):
> "We use two fungi: Trametes produces laccase enzymes that capture electrons, and Saccharomyces (brewer's yeast) donates electrons through its metabolism. Together, they create a living battery that generates 50-200 microwatts per square centimeter — enough to power a soil sensor for 7-14 days."

### The Solution (Slide 4):
> "Our value proposition is simple: Drop it. Monitor it. Forget it. No retrieval, no waste, no compliance headaches. The first battery that's designed to disappear."

### Market Opportunity (Slide 5):
> "This isn't a niche. The EU Battery Regulation creates a **mandated market** of €68 billion by 2030. If you're deploying sensors in Europe after 2026, and you can't retrieve them, you **have** to use something like MykoVolt."

### Competitive Advantage (Slide 6):
> "We have four defensible moats. Technical: Our AI pipeline accelerates R&D by 10x. Manufacturing: Compression molding gives us 100x the speed at 1/10th the cost. Regulatory: We'll be first to market with CE and FDA clearances. Data: Our platform creates network effects that get stronger with each sensor deployed."

### Financials (Slide 11):
> "We're raising €1.75 million to get us from PoC to pilot production. With this, we'll achieve €13.76 million in revenue by 2028, be ready for Series A, and target a €110 million valuation. The math is simple: EU regulations are creating demand, and we're the only ones who can supply it."

### Closing (Slide 15):
> "We're not just building a battery company. We're building the infrastructure for sustainable IoT. The question isn't whether the world needs this — the EU has already decided that it does. The question is: Will you be part of the solution?"

---

*Tip: Use Canva template "Midnight Blue + Green" for consistent branding. Color scheme: #2A3C44 (deep blue), #B8D4A0 (sage green), #F5F5F5 (off-white).*
