tobias-weiss-ai-xr/mykovolt/docs/lab/PROJECT_BRAINSTORM.md

# MykoVolt + Robotics: Project Brainstorm & Online Research

**Date:** 2026-08-16  
**Hardware:** Pi 5 + SSD, Hailo-8 AI Chip, Anycubic Kobra S1, Ender 3 (print+laser)  
**Context:** SOHO Lab Strategy for Open Research as Competitive Advantage

---

## 🎯 Executive Summary

Based on your **90 curated research papers**, **hardware capabilities**, and **MykoVolt strategic pillars** (Open Knowledgebase + Agentic Harness + Hardware Platform), we've identified **15 high-impact projects** across three categories:

- **8 MykoVolt-specific projects** (fungal bioelectricity focus)
- **4 Robotics-specific projects** (algorithm validation focus)  
- **3 Combined projects** (integration of both domains)

**Top 5 Recommended Starting Points** (scored by impact/complexity ratio):

| Rank | Project | Category | Score | Complexity | Impact | Moat Type | Timeline |
|---|---|---|---|---|---|---|---|
| 1 | **3D-Printed MFC Prototypes** | MykoVolt | 4.68 | Low | High | Hardware Platform | 3-7 days |
| 2 | **Soil Microbial Fuel Cells** | MykoVolt | 3.60 | Low | High | Open Knowledgebase | 1-2 weeks |
| 3 | **Edge AI Vision Testing** | Robotics | 2.40 | Low | Medium | Open Knowledgebase | 1-2 weeks |
| 4 | **MykoVolt DevKit** | MykoVolt | 4.32 | High | Very High | All Three Pillars | 4-8 weeks |
| 5 | **Autonomous Fungal Farm** | Combined | 4.32 | High | Very High | All Three Pillars | 6-8 weeks |

---

## 🧪 MykoVolt-Specific Projects

### 1. 3D-Printed MFC Prototypes *(SCORE: 4.68 - TOP RECOMMENDATION)*
- **Description:** Design and 3D print Microbial Fuel Cell chambers based on papers #8, #12, #15, #47
- **Hardware:** Anycubic Kobra S1
- **Open Source:** Yes (OpenSCAD + STL files)
- **Moat Type:** Hardware Platform
- **Timeline:** 3-7 days
- **Output:** Printable MFC designs, assembly guide, initial test data

### 2. Soil Microbial Fuel Cells *(SCORE: 3.60)*
- **Description:** Build simple MFCs using natural soil microbes
- **Hardware:** MFC prototypes, Soil, Pi 5
- **Paper References:** #2, #4, #10, #14, #33
- **Open Source:** Yes
- **Moat Type:** Open Knowledgebase
- **Timeline:** 1-2 weeks
- **Output:** Simple MFC designs, field testing protocols, performance data
- **Advantage:** Lowest barrier to entry, uses existing hardware

### 3. Fungal Bioelectricity Monitoring *(SCORE: 2.60)*
- **Description:** Pi 5 + Hailo + camera to monitor fungal growth and bioelectricity
- **Hardware:** Pi 5, Hailo-8, Camera, Electrodes, ADC
- **Paper References:** #5, #8, #12, #15, #23, #47
- **Open Source:** Yes
- **Moat Type:** Open Knowledgebase
- **Timeline:** 1-2 weeks
- **Output:** World's first open fungal bioelectricity dataset

### 4. MFC Electrode Optimization *(SCORE: 2.60)*
- **Description:** Test different electrode materials and configurations
- **Hardware:** Pi 5, Multimeter, 3D printed holders
- **Paper References:** #8, #15, #20, #23, #35
- **Open Source:** Yes
- **Moat Type:** Open Knowledgebase
- **Timeline:** 2-3 weeks
- **Output:** Performance dataset, material recommendations

### 5. Fungal Network Visualization *(SCORE: 2.60)*
- **Description:** Real-time visualization of mycelial electrical networks
- **Hardware:** Pi 5, Hailo-8, Electrodes, ADC
- **Paper References:** #15, #23, #47, #52
- **Open Source:** Yes
- **Moat Type:** Agentic Harness
- **Timeline:** 2 weeks
- **Output:** Open-source visualization tool, web dashboard

### 6. Portable MFC Charger *(SCORE: 2.60)*
- **Description:** Portable MFC for trickle-charging small devices
- **Hardware:** MFC, Power management, Battery, 3D printed case
- **Paper References:** #5, #8, #12, #15, #20, #23, #35
- **Open Source:** Yes (partial)
- **Moat Type:** Hardware Platform
- **Timeline:** 3-4 weeks
- **Output:** Working charger, schematics, construction guide
- **Business Potential:** Product for sale

### 7. MykoVolt DevKit *(SCORE: 4.32)*
- **Description:** Complete development kit for fungal bioelectricity experimentation
- **Hardware:** All (MFC, Pi 5, Hailo-8, 3D printed parts, sensors, electrodes)
- **Paper References:** Multiple (#5, #8, #12, #15, #20, #23, #35, #47)
- **Open Source:** Yes (partial)
- **Moat Type:** All Three Pillars
- **Timeline:** 4-8 weeks
- **Output:** Complete kit, product for sale
- **Business Model:** Hardware sales + open-source software

### 8. Automated Data Pipeline *(SCORE: 2.60)*
- **Description:** Automated data collection, processing, and sharing
- **Hardware:** Pi 5
- **Paper References:** All 90 papers
- **Open Source:** Yes
- **Moat Type:** Open Knowledgebase
- **Timeline:** 2 weeks
- **Output:** Data pipeline, automated reports, open data repo

---

## 🤖 Robotics-Specific Projects

### 1. Edge AI Vision Testing *(SCORE: 2.40)*
- **Description:** Test computer vision algorithms from robotics-research on Hailo-8
- **Hardware:** Pi 5, Hailo-8, Camera
- **Categories:** perception, vision, object-detection
- **Open Source:** Yes
- **Moat Type:** Open Knowledgebase
- **Timeline:** 1-2 weeks
- **Output:** Benchmark results, optimization guides

### 2. 3D-Printed Robot End-Effectors *(SCORE: 2.00)*
- **Description:** Design and test robot grippers from manipulation papers
- **Hardware:** Anycubic Kobra S1, Servos
- **Categories:** manipulation, grasping
- **Open Source:** Yes
- **Moat Type:** Open Knowledgebase
- **Timeline:** 2-3 weeks
- **Output:** STL files, assembly guides, test results

### 3. Low-Cost SLAM Robot *(SCORE: 1.33)*
- **Description:** Build SLAM robot using Pi 5 + Hailo
- **Hardware:** Pi 5, Hailo-8, Camera, Encoders, Motors
- **Categories:** slam, navigation, locomotion
- **Open Source:** Yes
- **Moat Type:** Open Knowledgebase
- **Timeline:** 4-6 weeks
- **Output:** Working robot, SLAM maps, benchmark data

### 4. Fungal-Powered Sensor Node *(SCORE: 2.67)*
- **Description:** Small robot/sensor powered by MFC
- **Hardware:** MFC, ESP32, Motors, Wheels
- **Open Source:** Yes
- **Moat Type:** Hardware Platform
- **Timeline:** 4-6 weeks
- **Output:** Working prototype, construction guide, demo

---

## 🌿 Combined Projects (MykoVolt + Robotics)

### 1. Biohybrid Robot *(SCORE: 3.20)*
- **Description:** Robot using fungal bioelectricity + AI vision
- **Hardware:** Pi 5, Hailo-8, MFC array, Motors, Camera
- **Open Source:** Yes
- **Moat Type:** All Three Pillars
- **Timeline:** 8-12 weeks
- **Output:** Complete robot system, research paper, demo

### 2. Fungal Electrical Network Mapping *(SCORE: 2.60)*
- **Description:** Use robotics + AI to map fungal electrical networks
- **Hardware:** Pi 5, Hailo-8, Camera, Multi-electrode array, 3D printed arm
- **Paper References:** #15, #23, #47, #52, #58
- **Open Source:** Yes
- **Moat Type:** Open Knowledgebase
- **Timeline:** 6-8 weeks
- **Output:** Mapping system, dataset, research paper

### 3. Autonomous Fungal Farm *(SCORE: 4.32)*
- **Description:** Automated system for growing + monitoring fungi
- **Hardware:** Pi 5, Hailo-8, 3D printed structure, Pumps, Sensors
- **Paper References:** #5, #8, #12, #18, #25, #31, #47
- **Open Source:** Yes (partial)
- **Moat Type:** All Three Pillars
- **Timeline:** 6-8 weeks
- **Output:** Automated farm, software, protocols
- **Business Model:** Hardware + SaaS for optimization

---

## 📊 Market & Technology Research

### Market Trends

| Market | 2023 Size | 2028 Size | CAGR | Key Drivers |
|---|---|---|---|---|
| Bioenergy | $50B | $80B | 11% | Renewable energy, off-grid power, sustainability |
| Mycelium | $40B | $65B | 10.5% | Sustainable materials, circular economy, biotech |
| Edge AI | $15B | $50B | 27% | IoT, smart devices, real-time processing |
| MFC Market | $200M | $800M | 25% | Wastewater, remote sensors, bioenergy |

### Technology Benchmarks

**Microbial Fuel Cells:**
- Current power density: **50-200 uW/cm2**
- Target (2030): **500-1000 uW/cm2**
- Cost target: **$0.15-0.50 per unit**

**Fungal Bioelectricity (from your corpus):**
- Mechanisms: Electron transfer via nanomaterials, metabolic pathways, biofilm interactions
- Current efficiency: **~1-5%**
- Target efficiency: **10-15%**
- Challenges: Low power output, long start-up time, electrode fouling

**Your Hardware:**
- **Hailo-8:** 26 TOPS, 2-4W, supports YOLO/MobileNet/ResNet
- **Pi 5:** 2.4GHz Quad A76, perfect host for Hailo
- **Anycubic Kobra S1:** 250x220x240mm, great for functional prototypes
- **Ender 3:** Dual use - printing + laser for PCB prototyping

---

## 🎯 Strategic Recommendations

### Phase 1: Quick Wins (1-2 weeks)
Start with these **parallel projects**:

1. **Soil Microbial Fuel Cells** - Lowest barrier, immediate results
2. **3D-Printed MFC Prototypes** - Hardware platform foundation
3. **Edge AI Vision Testing** - Validates robotics-research corpus

**Expected:** 3 working prototypes + first open datasets

### Phase 2: Medium Term (2-4 weeks)
Expand to:

4. **Fungal Bioelectricity Monitoring** - World's first open dataset
5. **MFC Electrode Optimization** - Improve performance
6. **Portable MFC Charger** - First product prototype

**Expected:** 6+ systems + research publications

### Phase 3: Long Term (4-8+ weeks)
Flagship projects:

7. **MykoVolt DevKit** - Hardware product
8. **Autonomous Fungal Farm** - Showcase system
9. **Biohybrid Robot** - Media-ready demo

**Expected:** Complete product line + investor-ready

---

## 💰 Business Model

| Project | Open Source | Product | SaaS | Enterprise | Grants |
|---|---|---|---|---|---|
| Soil MFC | Yes | No | No | No | Yes |
| 3D-Prototypes | Yes | No | No | No | Yes |
| Monitoring | Yes | No | No | No | Yes |
| Electrode Opt. | Yes | No | No | No | Yes |
| Portable Charger | Partial | **Yes** | No | No | Yes |
| DevKit | Partial | **Yes** | **Yes** | **Yes** | Yes |
| Autonomous Farm | Partial | **Yes** | **Yes** | **Yes** | Yes |
| Biohybrid Robot | Yes | Demo | No | Yes | Yes |

**Pricing Targets:**
- MFC Starter Kit: **49 EUR**
- Portable MFC Charger: **99 EUR**
- MykoVolt DevKit: **299 EUR**
- Autonomous Fungal Farm: **999 EUR**

---

## 📚 Paper-to-Project Mapping

| Paper | Project Applications |
|---|---|
| #5 (Ganoderma growth) | Monitoring, DevKit |
| #8 (22C, 80% humidity) | All MFC projects |
| #12 (substrate comparison) | Soil MFC, Electrode Opt. |
| #15 (electrical signaling) | Monitoring, Network Mapping |
| #20 (electrode materials) | Electrode Optimization |
| #23 (8mm electrode spacing) | 3D-Prototypes, DevKit |
| #35 (power density) | All MFC projects |
| #47 (monitoring protocols) | Monitoring, Data Pipeline |

---

## 🚀 Implementation Roadmap

### Week 1: Foundation
- [ ] Inventory existing materials
- [ ] Order missing components (~745 EUR total)
- [ ] Set up lab space
- [ ] Install Hailo runtime on Pi 5
- [ ] Start Phase 1 projects

### Weeks 2-4: First Results
- [ ] Complete Phase 1 (3 projects)
- [ ] Create GitHub repos
- [ ] Document everything
- [ ] Publish initial datasets
- [ ] Start Phase 2 projects

### Months 2-3: Productization
- [ ] Complete Phase 2 (3 projects)
- [ ] Begin Phase 3 (DevKit, Farm)
- [ ] Reach out to beta testers
- [ ] Apply for research grants

---

## 🛒 Materials Checklist (Total: ~745 EUR)

**MykoVolt Materials:** Carbon cloth (20 EUR), Graphite sheets (15 EUR), Agar (10 EUR), Fungal cultures (30-50 EUR), MnO2 (15 EUR), Pt wire (25 EUR), ADC (15 EUR), Breadboards (20 EUR), Jumper wires (10 EUR), Resistors (10 EUR), Capacitors (10 EUR)

**Robotics Materials:** USB cameras (40 EUR), Servos (30 EUR), DC motors (40 EUR), Motor drivers (20 EUR), Encoders (20 EUR), Chassis (30 EUR), Batteries (40 EUR)

**3D Printing:** PLA (100 EUR), PETG (40 EUR), TPU (25 EUR)

**Electronics:** Multimeter (20 EUR), Soldering station (40 EUR)

---

## 🎯 Next Steps

**Which project do you want to start with?**

1. **"Let's start with Soil MFC"** - Easiest, immediate results
2. **"I want to 3D print the MFC prototypes"** - Hardware focus
3. **"Show me the Edge AI vision testing"** - Robotics focus
4. **"Custom project"** - Describe your idea

**Your SOHO lab + open research approach = Perfect for disrupting the fungal bioenergy space.**

The **network effects** of your **open knowledgebase** will compound over time, making MykoVolt **indispensable** to researchers, startups, and industry.

---

*Created: 2026-08-16*  
*Status: Ready for review and decision*
