tobias-weiss-ai-xr/mykovolt/docs/outreach/cofounder_linkedin_post.md

# LinkedIn Post: CTO Co-Founder Search

---

**🍄 We're Hiring: Co-Founder / CTO for Deep Tech Climate Startup**

MykoVolt is building the **world's first biodegradable fungal bio-battery** for disposable IoT sensors. Think: sensors deployed like seeds — hundreds per hectare, fully buried, no retrieval. At end-of-life, the battery composts into the soil. Zero e-waste.

**The opportunity:**
- Ground-floor co-founder role in deep tech startup
- Lead prototype development (TRL 2→3)
- File patents, publish research, build defensible IP
- Funding pathway: EXIST → Horizon Europe → Series A
- Significant equity stake

**You bring:**
- PhD or M.Sc. in Fungal Biology, Electrochemistry, or Materials Science
- Hands-on lab skills (microbial cultivation, electrochemical characterization)
- Passion for sustainability, bioeconomy, climate tech
- Willing to relocate to Hesse, Germany (or remote + travel)

**You'll lead:**
- Prototype development (fungal MFC + cultivation)
- Master's thesis students (3-4 topics defined)
- Grant applications (EXIST, Horizon Europe, BMBF)
- Patent filings & scientific publications

**Current status:**
✅ Design & simulation complete
✅ FTO analysis: field is open (no blocking patents)
✅ Grant roadmap prepared
⏳ Recruiting CTO co-founder + Master's students
⏳ First prototype: Q4 2026 / Q1 2027

**Team:** Tobias (CIO: AI, simulation), Marc (Business Development), **you (CTO)**

**Why this matters:**
- 15+ applications across agriculture, construction, logistics
- €0.15/unit cost vs. €2-5 for Li-ion
- 90% biodegradable, zero retrieval labor
- Enables dense sensor networks previously impossible

**Location:** Hesse, Germany (Frankfurt/Rhein-Main area)
Lab work requires on-site presence. Remote possible for BD/grant work.

**📧 Apply:** tobias.weiss.ai.xr@gmail.com

Include:
1. CV / LinkedIn profile
2. Why MykoVolt? (2-3 sentences)
3. Availability (full-time, part-time, timeline)
4. Location / relocation plans

**🔗 Learn more:** github.com/tobias-weiss-ai-xr/mykovolt

---

#DeepTech #ClimateTech #Biotechnology #CircularEconomy #IoT #Sustainability #Bioeconomy #Startup #CoFounder #Hiring #GreenTech #Innovation #EWaste #FungalBiology #Electrochemistry #MaterialsScience #EXIST #HorizonEurope #Hesse #Germany

---

**P.S.** Also recruiting Master's thesis students (Q4 2026 / Q1 2027 start) — 10 topics across fungal strains, materials, electronics, and applications. See GitHub repo for details.
