tobias-weiss-ai-xr/mykovolt/docs/outreach/cofounder_outreach_email.md

# Direct Outreach Email Template: CTO Co-Founder

---

## Subject Line Options

- Co-Founder Opportunity: Deep Tech Climate Startup (Fungal Bio-Battery)
- CTO Co-Founder Search: MykoVolt — Biodegradable Battery for IoT
- Building the First Fungal Bio-Battery — Co-Founder Role

---

## Email Template

**Dear [Dr./Prof.] [First Name] [Last Name],**

I hope this message finds you well. My name is Tobias Weiß, and I'm the CIO/co-founder of **MykoVolt**, a deep tech climate startup building the world's first biodegradable fungal bio-battery for disposable IoT sensors.

**Why I'm reaching out:**

I came across your work on [specific paper/project/expertise area — e.g., "fungal electrochemistry" / "microbial fuel cells" / "biodegradable electronics"] and was impressed by [specific detail — e.g., "your 2023 paper on white-rot fungus laccase activity" / "your lab's work on compression-molded biocomposites"]. Your expertise aligns closely with what we're building at MykoVolt.

**What we're building:**

MykoVolt develops fungal microbial fuel cells (MFCs) that power IoT sensors in applications where batteries can't be retrieved and solar doesn't work: underground soil monitoring, concrete curing sensors, compost monitoring, cold-chain logistics, and more.

**Key value proposition:**
- 🍄 **Biodegradable:** 90% compostable (only electronics retrieved, reused 100+ cycles)
- 💰 **€0.15/unit cost** vs. €2-5 for Li-ion
- ♻️ **Zero e-waste:** No retrieval labor, no toxic waste
- 🌐 **15+ applications** across agriculture, construction, logistics, environment

**Current status:**
- ✅ Design & simulation complete (Empa baseline: 12.5 µW/cm²)
- ✅ FTO analysis: field is open (no blocking patents found)
- ✅ Grant roadmap prepared (Hessen Ideen, EXIST, Horizon Europe)
- ⏳ **Recruiting CTO co-founder** to lead prototype development
- ⏳ First prototype target: Q4 2026 / Q1 2027

**The opportunity:**

We're looking for a **Co-Founder / CTO** to lead:
- Prototype development (fungal MFC + cultivation)
- Master's thesis students (3-4 topics defined)
- Grant applications (EXIST, Horizon Europe, BMBF)
- Patent filings & scientific publications

**What you'd bring:**
- PhD or M.Sc. in Fungal Biology, Electrochemistry, or Materials Science
- Hands-on lab skills (microbial cultivation, electrochemical characterization)
- Passion for sustainability, bioeconomy, climate tech
- Willing to relocate to Hesse, Germany (or remote + travel for lab work)

**What you'd get:**
- Significant co-founder equity stake
- Ground-floor role in deep tech startup with clear funding pathway
- IP creation from day 1 (patents, publications)
- Real climate impact (e-waste reduction, sustainable IoT)

**Team:**
- **Tobias (me):** CIO — AI, simulation, business development
- **Marc:** Business Development — partnerships, grant strategy (part-time)
- **You:** CTO — fungal biology, electrochemistry, prototype lead

**Location:** Hesse, Germany (Frankfurt/Rhein-Main area). Lab work requires on-site presence; grant/BD work can be remote.

**Next steps:**

If this sounds interesting, I'd love to schedule a brief call (30 min) to discuss:
1. Your background and interests
2. MykoVolt's technology and roadmap in more detail
3. Potential fit as co-founder

Are you available for a call sometime in the next 1-2 weeks? I'm flexible on timing and can work around your schedule.

**Learn more:**
- GitHub: github.com/tobias-weiss-ai-xr/mykovolt
- LinkedIn: linkedin.com/company/mykovolt

Looking forward to hearing from you!

Best regards,

**Tobias Weiß**
Co-Founder & CIO, MykoVolt
📧 tobias.weiss.ai.xr@gmail.com
📱 +49 177 9132333
🔗 linkedin.com/in/tobias-weiss-ai-xr

---

## Personalization Tips

**Before sending, customize:**

1. **Research the person:**
   - Read their recent papers (last 2-3 years)
   - Check their lab website / Google Scholar
   - Note any relevant projects (MFCs, fungal biology, biodegradable materials, electrochemistry)

2. **Personalize the opening:**
   - Mention a specific paper, project, or talk
   - Explain why their expertise is uniquely relevant
   - Show you've done your homework

3. **Adjust for background:**
   - **Academic researcher:** Emphasize publications, IP, lab autonomy
   - **Industry professional:** Emphasize commercial potential, market size, exit scenarios
   - **PhD student/postdoc:** Emphasize career growth, equity, building from ground up

4. **Add mutual connections (if any):**
   - "We both know [Name] from [context]"
   - "[Name] suggested I reach out"

---

## Follow-Up Sequence

**If no response after 5-7 days:**

### Follow-Up 1 (Day 7)
**Subject:** Re: Co-Founder Opportunity: MykoVolt

Hi [Name],

Just wanted to follow up on my previous email about the CTO co-founder role at MykoVolt. I know you're busy, so I'll keep this brief.

We're building a biodegradable fungal battery for IoT sensors — design complete, recruiting team to build first prototype Q4 2026. Your work on [specific area] would be incredibly valuable.

Happy to schedule a quick 15-min call if you're curious. No pressure if timing doesn't work.

Best,
Tobias

---

### Follow-Up 2 (Day 14)
**Subject:** Quick question

Hi [Name],

One last ping on this — if the co-founder role isn't the right fit, would you be open to an advisory role (2-4 hours/week)? Or do you know anyone in your network who might be interested?

Either way, appreciate your time.

Best,
Tobias

---

## Target List Suggestions

**Universities/Institutes to target:**

| Institution | Department/Center | Why Relevant |
|---|---|---|
| JLU Gießen | Institut für Mikrobiologie & Biotechnologie | Fungal biology, mycology |
| JLU Gießen | Institut für Physikalische Chemie | Electrochemistry |
| TU Darmstadt | Fachbereich Biologie | Microbial biotechnology |
| TU Darmstadt | Fachbereich Materialwissenschaft | Biodegradable materials |
| Uni Marburg | SYNMIKRO | Synthetic microbiology |
| KIT Karlsruhe | Institut für Biologische Grenzflächen | Bio-electrochemistry |
| Empa (CH) | Functional Materials Laboratory | Already published on fungal MFCs |
| Max Planck Institutes | Various | Deep expertise, potential advisors |

**LinkedIn search terms:**
- "fungal biology" + Germany
- "electrochemistry" + biodegradable
- "microbial fuel cell" researcher
- "biodegradable electronics"
- "materials science" + bio-based

---

## Response Handling

**If interested:**
1. Schedule 30-min video call within 1 week
2. Send calendar invite with Zoom/Meet link
3. Prepare pitch deck (PITCH_DECK.html) for call
4. After call: send follow-up with next steps (in-person meeting, technical deep-dive)

**If not interested but offers referral:**
1. Thank them warmly
2. Ask for introduction to referred person
3. Keep them in loop as potential advisor

**If not interested:**
1. Thank them for their time
2. Ask if open to advisory role (2-4 hrs/week)
3. Ask permission to stay in touch for future collaboration
4. Add to "keep warm" list (quarterly updates)
