tobias-weiss-ai-xr/mykovolt/docs/outreach/cofounder_twitter_thread.md

# Twitter/X Thread: CTO Co-Founder Search

---

**Tweet 1/7**
🍄 We're hiring a Co-Founder/CTO for our deep tech climate startup!

MykoVolt is building the world's first biodegradable fungal bio-battery for IoT sensors.

Think: sensors deployed like seeds 🌱
- Fully buried
- No retrieval needed
- Composts at end-of-life
- Zero e-waste ♻️

---

**Tweet 2/7**
The problem:

Millions of disposable IoT sensors use Li-ion batteries that:
❌ Create toxic e-waste
❌ Require costly retrieval
❌ Fail underground/in darkness (solar useless)

Our solution:

Living fungi generate power 🍄⚡
- Yeast (anode) + white-rot fungus (cathode)
- Cellulose matrix, compression-molded
- Activated with water + nutrients

---

**Tweet 3/7**
Market opportunity:

15+ applications across:
🌾 Precision agriculture
🏗️ Construction (concrete curing)
📦 Cold-chain logistics
🗑️ Compost monitoring
❄️ Permafrost sensing
🌲 Forestry (under-canopy)

€0.15/unit vs €2-5 for Li-ion
90% biodegradable

---

**Tweet 4/7**
Current status:

✅ Design & simulation complete
✅ FTO analysis: field is OPEN (no blocking patents!)
✅ Grant roadmap ready (EXIST, Horizon Europe)
⏳ Recruiting CTO co-founder
⏳ First prototype: Q4 2026 / Q1 2027

Team: Tobias (CIO), Marc (BD), YOU (CTO)

---

**Tweet 5/7**
You bring:
- PhD/M.Sc. in Fungal Biology, Electrochemistry, or Materials Science
- Hands-on lab skills
- Passion for climate tech & bioeconomy
- Based in/relocate to Hesse, Germany

You'll lead:
- Prototype development
- Master's students (3-4 topics)
- Grants, patents, publications

---

**Tweet 6/7**
Why this matters:

Deep tech = long game (5-7 yrs to market)
But:
🎯 Ground-floor equity
🎯 Real climate impact
🎯 IP creation from day 1
🎯 Funding pathway clear (non-dilutive first)
🎯 Build something that matters

Location: Hesse, Germany (Frankfurt/Rhein-Main)

---

**Tweet 7/7**
📧 Apply: tobias.weiss.ai.xr@gmail.com

Include:
1. CV/LinkedIn
2. Why MykoVolt? (2-3 sentences)
3. Availability
4. Location/relocation plans

🔗 github.com/tobias-weiss-ai-xr/mykovolt

#DeepTech #ClimateTech #Biotech #CircularEconomy #Hiring #CoFounder

---

## Posting Instructions

**Best practices:**
- Post all 7 tweets as a thread (use Twitter's thread feature)
- Attach the SVG image to Tweet 1
- Post Tuesday-Thursday, 9-11 AM or 1-3 PM (best engagement)
- Pin the thread to your profile for 2-4 weeks
- Retweet with comment after 24 hours for additional reach

**Engagement boost:**
- Tag relevant accounts: @HessenAgentur, @EXIST_Gruenden, @EU_Commission, @ClimateKIC
- Reply to each tweet within 1 hour of posting (boosts algorithm)
- Share in relevant Slack/Discord communities after posting
