tobias-weiss-ai-xr/mykovolt/docs/outreach/join_us.md

# Join MykoVolt — Building the First Fungal Bio-Battery

## What We're Building

**MykoVolt** develops the world's first biodegradable fungal bio-battery for disposable IoT sensors. Our technology enables **drop-and-forget sensor networks** that operate underground, in darkness, and compost away at end-of-life — zero e-waste, zero retrieval required.

**The vision:** Sensors deployed like seeds — hundreds per hectare, fully buried, no retrieval. At end-of-life, the battery and housing compost into the soil; only the electronics board is retrieved (100+ reuse cycles).

---

## Current Status (July 2026)

- ✅ **Design complete** (MFC architecture, electronics, firmware)
- ✅ **Simulation validated** (Empa baseline: 12.5 µW/cm²)
- ✅ **Grant roadmap prepared** (Hessen Ideen, EXIST)
- ✅ **Master's thesis topics defined** (10 topics across 5 work packages)
- ✅ **Business Development:** Marc (part-time)
- ❌ **Team: Looking for co-founders (CTO) + students**
- ❌ **Prototype: Not yet built**

**Next milestone:** Build first functional prototype (Q4 2026 - Q1 2027).

---

## Team

### Business Development
- **Marc** — Business development, partnerships, grant strategy (part-time)

### AI & Simulation
- **Tobias** — CIO, AI, simulation, business development

### Open Roles

### 1. Co-Founder / CTO (Technical Lead)

**Profile:**
- PhD or M.Sc. + experience in **fungal biology, electrochemistry, or materials science**
- Hands-on lab skills (microbial cultivation, electrochemical characterization)
- Interest in deep tech startups, sustainability, bioeconomy
- Willing to relocate to Hesse, Germany (or remote + travel)

**Responsibilities:**
- Lead prototype development (MFC pellet + fungal cultivation)
- Supervise Master's thesis students (WP1: Fungal Strains, WP2: Materials)
- File patents, publish papers
- Apply for grants (Hessen Ideen, EXIST, Horizon Europe)

**Equity:** Significant co-founder equity (to be discussed)

---

### 2. Co-Founder / CEO (Business Lead)

**Note:** Marc is supporting business development. We're still looking for a dedicated CEO co-founder to lead fundraising and operations full-time.

**Profile:**
- M.Sc. or MBA + experience in **business development, fundraising, grant writing**
- Track record: startups, consulting, or corporate strategy (cleantech/biotech preferred)
- Network: investors, grant agencies, industry partners
- Willing to relocate to Hesse, Germany (or remote + travel)

**Responsibilities:**
- Grant applications (Hessen Ideen, EXIST, Horizon Europe)
- Investor relations (pre-seed, seed, Series A)
- Customer development (pilot partners, LOIs)
- Team building, operations, legal

**Equity:** Significant co-founder equity (to be discussed)

---

### 3. Master's Thesis Students (Q4 2026 / Q1 2027 Start)

**10 thesis topics** across 5 work packages. Key priorities:

#### WP2.1: Compression-Molded Fungal MFC Pellets *(Critical Path)*
**Degree:** M.Sc. Materials Science / Chemical Engineering
**Start:** Q4 2026 / Q1 2027
**Task:** Build first compression-molded MFC prototype
**Supervision:** Co-founder (CTO) + university professor

#### WP3.1: Ultra-Low-Power MCU Firmware *(Critical Path)*
**Degree:** M.Sc. Electrical Engineering / Embedded Systems
**Start:** Q4 2026 / Q1 2027
**Task:** Build first working sensor node (STM32L0 + boost converter)
**Supervision:** Co-founder (CTO) + university professor

#### WP1.1: High-Performance Fungal Strains
**Degree:** M.Sc. Biotechnology / Microbiology
**Start:** Q4 2026 / Q1 2027
**Task:** Screen fungal strains, reproduce Empa baseline (12.5 µW/cm²)
**Supervision:** Co-founder (CTO) + university professor

**More topics:** See [`docs/masters_thesis_topics.md`](docs/masters_thesis_topics.md)

**Funding:** €500-1000/month stipend (if grant-funded) or university-funded
**IP:** MykoVolt retains IP; student is named inventor + first author on papers

---

### 4. Advisors / Supporting Roles

**Looking for:**
- **Fungal biology experts** (strain selection, cultivation protocols)
- **Electrochemists** (MFC characterization, enzyme kinetics)
- **Materials scientists** (compression molding, biodegradable polymers)
- **Embedded systems engineers** (ultra-low-power design, boost converters)
- **Grant writers** (Hessen Ideen, EXIST, Horizon Europe experience)

**Commitment:** 2-4 hours/week, advisory role, equity or honorarium

---

## Why Join?

### For Co-Founders

- **Ground-floor opportunity:** Build a deep tech startup from day one
- **Meaningful mission:** Solve e-waste, enable sustainable IoT, fight climate change
- **IP creation:** File patents, publish papers, build defensible technology
- **Funding pathway:** Hessen Ideen → EXIST → Horizon Europe → Series A
- **Equity:** Significant co-founder stake (to be discussed)

### For Master's Students

- **Real-world impact:** Your thesis builds the **first functional prototype**
- **Publications:** Peer-reviewed papers (first author)
- **IP experience:** Named inventor on patents
- **Career launchpad:** Deep tech startup experience, network, references
- **Funding:** €500-1000/month stipend (if grant-funded)

### For Advisors

- **Shape early-stage technology:** Influence R&D direction
- **Equity or honorarium:** Compensation for contributions
- **Publication opportunities:** Co-author on papers
- **Network:** Connect with founders, investors, researchers

---

## How to Apply

### Co-Founders (CEO / CTO)

**Send to:** tobias.weiss.ai.xr@gmail.com

**Include:**
1. CV / LinkedIn profile
2. Why MykoVolt? (2-3 sentences)
3. What role interests you (CEO, CTO, or both)
4. Availability (full-time, part-time, timeline)
5. Location / relocation plans

**Process:**
1. Email → 2. Video call (30 min) → 3. In-person meeting → 4. Co-founder agreement

---

### Master's Thesis Students

**Send to:** tobias.weiss.ai.xr@gmail.com

**Include:**
1. CV + transcript (current GPA)
2. Which thesis topic(s) interest you (see [`docs/masters_thesis_topics.md`](docs/masters_thesis_topics.md))
3. Your university + expected graduation date
4. Relevant skills (lab work, programming, electronics, etc.)
5. Why MykoVolt? (2-3 sentences)

**Process:**
1. Email → 2. Video call (30 min) → 3. Thesis proposal → 4. Start date

**Timeline:**
- **Q3 2026:** Post openings, recruit
- **Q4 2026:** Interview, onboard (for Q1 2027 start)
- **Q1 2027:** Thesis begins (prototype build)

---

### Advisors

**Send to:** tobias.weiss.ai.xr@gmail.com

**Include:**
1. CV / LinkedIn profile
2. Area of expertise
3. Availability (hours/week)
4. How you can help MykoVolt

---

## FAQ

**Q: Where is MykoVolt based?**
A: Hesse, Germany (Frankfurt/Rhein-Main area). Remote is possible for co-founders, but lab work requires on-site presence.

**Q: Is this a university spinoff?**
A: Potentially. If co-founders are affiliated with a university (Empa, TU Darmstadt, KIT, etc.), we'll structure as a spinoff. Otherwise, we're an independent startup.

**Q: What's the funding status?**
A: Pre-seed. Currently preparing Hessen Ideen (€50k-150k) and EXIST (€250k-500k) applications. Master's thesis stipends depend on grant success (or university funding).

**Q: What if I'm interested but can't commit full-time?**
A: Advisor role is flexible (2-4 hours/week). Co-founders should commit full-time eventually, but part-time transition is possible initially.

**Q: Can I work remotely?**
A: Yes for business development, grant writing, software. Lab work (fungal cultivation, electrochemistry) requires on-site presence.

---

## Contact

- **Email:** tobias.weiss.ai.xr@gmail.com
- **GitHub:** [tobias-weiss-ai-xr/mykovolt](https://github.com/tobias-weiss-ai-xr/mykovolt)
- **LinkedIn:** [MykoVolt](https://www.linkedin.com/company/mykovolt)
- **Twitter:** [@MykoVolt](https://twitter.com/MykoVolt)

---

*Last updated: 2026-07-20 (Q3 2026)*
