tobias-weiss-ai-xr/mykovolt/docs/superpowers/plans/2025-06-29-mykolt-v2-mvp-improvements.md

# MykoVolt MVP Improvements Implementation Plan

> **For agentic workers:** REQUIRED SUB-SKILL: Use superpowers:subagent-driven-development (recommended) or superpowers:executing-plans to implement this plan task-by-task. Steps use checkbox (`- [ ]`) syntax for tracking.

**Goal:** Transform the risky MVP design into a validated, market-ready product through systematic risk mitigation and business model refinement.

**Architecture:** Phased approach addressing technical validation, business model refinement, regulatory compliance, and MVP validation in sequential sprints to ensure each phase delivers measurable value while reducing risk.

**Tech Stack:** Python (scikit-learn, scipy, networkx), C++ (STM32), Docker, pytest, Git, Markdown documentation

---

## Project Overview & Risk Summary

**Critical Risks Identified:**
- Technical: Unvalidated battery performance assumptions, single-source component dependencies
- Business: Over-simplified customer segmentation, funding concentration risk
- Regulatory: No EU Battery Regulation compliance strategy
- IP: No intellectual property protection strategy
- Market: Competitive landscape not analyzed

**Total Project Duration:** 12 months
**Total Budget:** €500,000 (including contingency)

---

## Phase 1: Technical Validation & Risk Mitigation (Months 1-3)

### Task 1: Battery Performance Validation Rig
**Files:**
- `tests/battery_validation.py`
- `simulation/battery_test_harness.py`
- `docs/validation_protocol.md`
- `README.md` (updated with validation results)

**Steps:**
1. [ ] **Step 1: Write validation test framework**
```python
def test_battery_performance():
    # Load both fungal strains
    t_pubescens_data = load_strain_data('T_pubescens')
    p_chrysosporium_data = load_strain_data('P_chrysosporium')
    
    # Test power output under controlled conditions
    t_power = calculate_power_output(t_pubescens_data, temp=25, humidity=60)
    p_power = calculate_power_output(p_chrysosporium_data, temp=25, humidity=60)
    
    # Validate against projections
    assert abs(t_power - 12.5) / 12.5 < 0.2  # Within 20%
    assert p_power > 150  # At least 150 µW/cm²
```

2. [ ] **Step 2: Run validation tests**
```bash
pytest tests/battery_validation.py -v
Expected: PASS with validated performance ranges
```

3. [ ] **Step 3: Build test rig hardware interface**
```python
class BatteryTestRig:
    def __init__(self):
        self.temperature_control = TemperatureController()
        self.humidity_control = HumidityController()
        self.data_acquisition = DataAcquisitionSystem()
    
    def run_test(self, strain, duration_hours):
        self.temperature_control.set_temp(25)
        self.humidity_control.set_humidity(60)
        return self.collect_power_data(strain, duration_hours)
```

4. [ ] **Step 4: Validate and document results**
```bash
git add tests/battery_validation.py simulation/battery_test_harness.py

git commit -m "feat: implement battery performance validation"
```

### Task 2: Component Redundancy Planning
**Files:**
- `docs/supply_chain_analysis.md`
- `simulation/component_failure_modes.py`
- `src/alternative_architectures/`
- `README.md` (updated with component alternatives)

**Steps:**
1. [ ] **Step 1: Research component alternatives**
```python
# Alternative NFC chips
NFC_ALTERNATIVES = {
    'ST25DV04K': {'cost': 1.20, 'availability': 'medium'},
    'NT3H2513': {'cost': 0.95, 'availability': 'high'},
    'M24SR64': {'cost': 1.10, 'availability': 'medium'}
}

# Alternative STM32L011
MCU_ALTERNATIVES = {
    'STM32L011K4': {'cost': 1.50, 'sleep_current': 1.8},
    'STM32L0522': {'cost': 2.10, 'sleep_current': 0.8},
    'NRF52832': {'cost': 3.50, 'sleep_current': 0.5}
}
```

2. [ ] **Step 2: Design simplified board versions**
```python
class AlternativeDevKit:
    def __init__(self, nfc_chip='NT3H2513', mcu='STM32L0522'):
        self.nfc = NFCController(nfc_chip)
        self.mcu = MCUController(mcu)
        self.power_manager = PowerManager()
    
    def get_estimated_cost(self):
        return self.nfc.cost + self.mcu.cost + self.power_manager.cost
```

3. [ ] **Step 3: Document component lead times and availability**
```python
SUPPLY_CHAIN_DATA = {
    'ST25DV04K': {'lead_time_weeks': 6, 'risk_level': 'high'},
    'NT3H2513': {'lead_time_weeks': 3, 'risk_level': 'low'},
    'STM32L011K4': {'lead_time_weeks': 4, 'risk_level': 'medium'},
    'STM32L0522': {'lead_time_weeks': 2, 'risk_level': 'low'}
}
```

4. [ ] **Step 4: Update documentation**
```bash
git add docs/supply_chain_analysis.md
git commit -m "docs: document component redundancy strategy"
```

### Task 3: Pilot Production Line Setup
**Files:**
- `production/pilot_production.py`
- `docs/manufacturing_process.md`
- `simulation/production_yield_analysis.py`
- `README.md` (updated with manufacturing details)

**Steps:**
1. [ ] **Step 1: Set up production environment**
```python
class PilotProduction:
    def __init__(self):
        self.tablet_press = TabletPress(capacity=50)  # units/day
        self.drying_oven = DryingOven(temperature=40)
        self.vacuum_sealer = VacuumSealer()
        self.quality_control = QualityControl()
    
    def produce_batch(self, quantity):
        tablets = self.tablet_press.press(quantity)
        dried = self.drying_oven.dry(tablets)
        sealed = self.vacuum_sealer.seal(dried)
        return self.quality_control.inspect(sealed)
```

2. [ ] **Step 2: Test production parameters**
```python
def test_production_parameters():
    # Test different press speeds and pressures
    for pressure in [10, 20, 30, 40, 50]:
        for speed in [10, 20, 30]:
            yield = run_production_test(pressure, speed)
            if yield > 0.95:  # >95% yield
                return pressure, speed, yield
    
    raise Exception("No optimal production parameters found")
```

3. [ ] **Step 3: Document actual costs**
```python
PRODUCTION_COSTS = {
    'tablet_press': 800,
    'drying_oven': 300,
    'vacuum_sealer': 200,
    'quality_control': 150,
    'materials_per_unit': 0.50
}

def calculate_total_cost(units):
    equipment_amortized = sum(PRODUCTION_COSTS[k] for k in ['tablet_press', 'drying_oven', 'vacuum_sealer', 'quality_control']) / 1000
    material_cost = units * PRODUCTION_COSTS['materials_per_unit']
    return equipment_amortized + material_cost
```

4. [ ] **Step 4: Update project documentation**
```bash
git add production/pilot_production.py docs/manufacturing_process.md
git commit -m "feat: implement pilot production line"
```

---

## Phase 2: Business Model Refinement (Months 4-6)

### Task 4: Customer Segment Strategy Development
**Files:**
- `marketing/segment_strategies.md`
- `sales/customer_profiles.md`
- `pricing/segment_pricing.py`
- `README.md` (updated with go-to-market strategy)

**Steps:**
1. [ ] **Step 1: Create detailed customer profiles**
```python
CUSTOMER_PROFILES = {
    'research_labs': {
        'budget': 5000,
        'decision_makers': ['principal_investigator', 'department_head'],
        'features_priority': ['accuracy', 'data_export', 'technical_support'],
        'expected_lifespan': '3-5 years'
    },
    'universities': {
        'budget': 3000,
        'decision_makers': ['department_chair', 'research_fellow'],
        'features_priority': ['educational_value', 'curriculum_integration'],
        'expected_lifespan': '2-4 years'
    },
    'farmers': {
        'budget': 150,
        'decision_makers': ['farm_manager', 'agricultural_consultant'],
        'features_priority': ['ease_of_use', 'battery_life', 'data_visualization'],
        'expected_lifespan': '1-2 years'
    }
}
```

2. [ ] **Step 2: Develop segment-specific value propositions**
```python
SEGMENT_VALUE_PROPOSITIONS = {
    'research_labs': 'Validated, research-grade soil moisture sensing with published performance data',
    'universities': 'Educational tool for soil science with curriculum integration',
    'farmers': 'Low-cost, long-lasting soil moisture monitoring for precision agriculture'
}
```

3. [ ] **Step 3: Create pricing strategies**
```python
def calculate_segment_price(segment, quantity):
    base_prices = {
        'research_labs': 35,
        'universities': 25,
        'farmers': 15
    }
    
    volume_discounts = {
        'research_labs': {100: 0.05, 500: 0.10, 1000: 0.15},
        'universities': {50: 0.08, 200: 0.12, 500: 0.18},
        'farmers': {10: 0.05, 50: 0.10, 100: 0.15}
    }
    
    price = base_prices[segment] * quantity
    discount = volume_discounts[segment].get(quantity, 0)
    return price * (1 - discount)
```

4. [ ] **Step 4: Update marketing materials**
```bash
git add marketing/segment_strategies.md pricing/segment_pricing.py
git commit -m "feat: develop customer segment strategies"
```

### Task 5: Diversified Funding Strategy
**Files:**
- `finance/funding_strategy.md`
- `business_model/revenue_streams.py`
- `docs/investor_deck_structure.md`
- `README.md` (updated with funding plan)

**Steps:**
1. [ ] **Step 1: Map all potential funding sources**
```python
FUNDING_SOURCES = {
    'EXIST_grant': {
        'amount': 15000,
        'timeline': 'Q3 2026',
        'requirements': ['feasibility_study', 'team_experience'],
        'risk_level': 'medium'
    },
    'Horizon_Europe_CL6': {
        'amount': 120000,
        'timeline': 'Q4 2026',
        'requirements': ['scalability_plan', 'market_analysis'],
        'risk_level': 'high'
    },
    'Angel_Investors': {
        'amount': 50000,
        'timeline': 'Q2 2026',
        'requirements': ['traction_metrics', 'team'],
        'risk_level': 'medium'
    },
    'Customer_Preorders': {
        'amount': 25000,
        'timeline': 'Q4 2026',
        'requirements': ['minimum_viable_product'],
        'risk_level': 'low'
    }
}
```

2. [ ] **Step 2: Develop contingency timeline**
```python
def create_funding_timeline():
    timeline = []
    for source in FUNDING_SOURCES.values():
        timeline.append({
            'source': source['amount'],
            'timeline': source['timeline'],
            'contingency': 'backup_plan' if source['risk_level'] == 'high' else 'primary'
        })
    return timeline
```

3. [ ] **Step 3: Create bootstrap runway calculation**
```python
def calculate_bootstrap_needs():
    monthly_expenses = {
        'personnel': 15000,
        'equipment': 3000,
        'materials': 2000,
        'marketing': 5000,
        'overhead': 2000
    }
    
    total_monthly = sum(monthly_expenses.values())
    runway_months = 12  # 12 months of runway
    
    return {
        'monthly_burn_rate': total_monthly,
        'desired_runway': runway_months,
        'bootstrap_requirement': total_monthly * runway_months,
        'funding_gap': 500000 - total_monthly * runway_months
    }
```

4. [ ] **Step 4: Document investment strategy**
```bash
git add finance/funding_strategy.md business_model/revenue_streams.py
git commit -m "feat: develop diversified funding strategy"
```

---

## Phase 3: Regulatory & IP Protection (Months 7-9)

### Task 6: Regulatory Compliance Framework
**Files:**
- `compliance/regulatory_roadmap.md`
- `docs/eu_battery_regulation_analysis.md`
- `tests/regulatory_compliance.py`
- `README.md` (updated with compliance requirements)

**Steps:**
1. [ ] **Step 1: Analyze EU Battery Regulation requirements**
```python
EU_BATTERY_REGULATION = {
    'substance_restrictions': ['lead', 'mercury', 'cadmium', 'hexavalent_chromium'],
    'weight_limits': {
        'portable_batteries': '< 1000g',
        'industrial_batteries': '< 10kg',
        'vehicle_batteries': '< 500kg'
    },
    ' labeling_requirements': ['capacity', 'energy', 'weight', 'hazard_symbols'],
    'collection_targets': {
        'portable_batteries': '45%',
        'rechargeable_batteries': '65%',
        'electric_vehicle_batteries': '85%'
    }
}
```

2. [ ] **Step 2: Develop compliance testing protocol**
```python
class RegulatoryComplianceTester:
    def __init__(self):
        self.substance_analyzer = SubstanceAnalyzer()
        self.weight_measurer = WeightMeasurer()
        self.label_validator = LabelValidator()
        self.recycling_test = RecyclingTest()
    
    def run_compliance_tests(self):
        results = {}
        results['substance_compliance'] = self.substance_analyzer.analyze(EU_BATTERY_REGULATION['substance_restrictions'])
        results['weight_compliance'] = self.weight_measurer.check(EU_BATTERY_REGULATION['weight_limits'])
        results['label_compliance'] = self.label_validator.validate(EU_BATTERY_REGULATION['labeling_requirements'])
        results['recycling_compliance'] = self.recycling_test.measure(EU_BATTERY_REGULATION['collection_targets'])
        return results
```

3. [ ] **Step 3: Create exemption application strategy**
```python
REGULATORY_EXEMPTION_STRATEGY = {
    'biodegradable_batteries': {
        'basis': 'Reduced environmental impact',
        'evidence_required': ['comprehensive_degradation_study', 'lifecycle_analysis'],
        'timeline': '6-9 months',
        'success_probability': 0.7
    },
    'agricultural_equipment': {
        'basis': 'Essential agricultural equipment exemption',
        'evidence_required': ['agricultural_validation_study', 'field_test_results'],
        'timeline': '3-6 months',
        'success_probability': 0.8
    }
}
```

4. [ ] **Step 4: Document reporting requirements**
```bash
git add compliance/regulatory_roadmap.md tests/regulatory_compliance.py
git commit -m "feat: implement regulatory compliance framework"
```

### Task 7: IP Protection Strategy
**Files:**
- `ip/ip_strategy.md`
- `docs/patent_portfolio_plan.md`
- `legal/ip_monitoring.py`
- `README.md` (updated with IP strategy)

**Steps:**
1. [ ] **Step 1: Identify patentable inventions**
```python
PATENTABLE_INVENTIONS = {
    'pressing_process': {
        'description': 'Novel fungal cell pressing technique for MFC tablet production',
        'novelty': 'New combination of pressure, moisture, and drying parameters',
        'inventive_step': 'Achieves 95%+ yield with standard equipment',
        'industrial applicability': 'Scalable to 10,000+ units/day'
    },
    'power_management_algorithm': {
        'description': 'Adaptive power management for fungal bio-batteries',
        'novelty': 'Dynamic optimization based on real-time performance',
        'inventive_step': 'Extends battery life by 300% vs. traditional methods',
        'industrial applicability': 'Applicable to all MFC systems'
    },
    'data_integration_system': {
        'description': 'NFC-to-cloud data integration with quality control',
        'novelty': 'Combines hardware, firmware, and cloud software',
        'inventive_step': 'Real-time quality assurance and data validation',
        'industrial applicability': 'Scalable to thousands of devices'
    }
}
```

2. [ ] **Step 2: Develop filing strategy**
```python
class IPFilingStrategy:
    def __init__(self):
        self.priority_patents = []
        self.followon_patents = []
        self.trade_secrets = []
        self.Copyrights = []
    
    def create_filing_schedule(self):
        schedule = {
            'month_3': {
                'action': 'file provisional patents',
                'inventions': ['pressing_process', 'power_management_algorithm'],
                'budget': 15000
            },
            'month_6': {
                'action': 'file international patents',
                'inventions': ['pressing_process', 'power_management_algorithm', 'data_integration_system'],
                'budget': 50000
            },
            'month_9': {
                'action': 'file utility patents',
                'inventions': ['data_integration_system'],
                'budget': 20000
            }
        }
        return schedule
```

3. [ ] **Step 3: Create licensing strategy**
```python
def create_licensing_strategy():
    licensing_terms = {
        'manufacturing_license': {
            'fee': '€50,000 upfront + 5% royalty',
            'territory': 'Global',
            'duration': '10 years',
            'exclusivity': 'Non-exclusive'
        },
        'technology_license': {
            'fee': '€25,000 upfront + 3% royalty',
            'territory': 'Global',
            'duration': '15 years',
            'exclusivity': 'Non-exclusive'
        },
        'knowhow_license': {
            'fee': '€10,000 annually',
            'territory': 'Global',
            'duration': '5 years',
            'exclusivity': 'Non-exclusive'
        }
    }
    return licensing_terms
```

4. [ ] **Step 4: Establish monitoring procedures**
```bash
git add ip/ip_strategy.md legal/ip_monitoring.py
git commit -m "feat: implement IP protection strategy"
```

---

## Phase 4: MVP Validation (Months 10-12)

### Task 8: MVP Validation Prototype
**Files:**
- `prototype/mvp_prototype.py`
- `tests/mvp_validation.py`
- `docs/validation_results.md`
- `README.md` (updated with prototype results)

**Steps:**
1. [ ] **Step 1: Build functional prototype**
```python
class MVPPrototype:
    def __init__(self):
        self.pressing_system = PressingSystem()
        self.electronics_board = ElectronicsBoard()
        self.nfc_reader = NFCReader()
        self.power_management = PowerManagement()
        self.data_storage = DataStorage()
    
    def assemble_device(self):
        device = {
            'pressing_system': self.pressing_system.assemble(),
            'electronics': self.electronics_board.assemble(),
            'communication': self.nfc_reader.assemble(),
            'power': self.power_management.assemble(),
            'storage': self.data_storage.assemble()
        }
        return device
    
    def test_functionality(self):
        test_results = []
        test_results.append(self.test_pressing_system())
        test_results.append(self.test_electronics())
        test_results.append(self.test_communication())
        test_results.append(self.test_power_system())
        test_results.append(self.test_data_storage())
        return all(test_results)
```

2. [ ] **Step 2: Test with target customers**
```python
def customer_validation_testing():
    test_customers = [
        ('research_lab', create_research_lab_test()),
        ('university', create_university_test()),
        ('farmer', create_farmer_test())
    ]
    
    validation_results = []
    for customer_type, test in test_customers:
        results = test.run()
        validation_results.append({
            'customer_type': customer_type,
            'satisfaction': results['satisfaction_score'],
            'functionality': results['functionality_score'],
            'value_perception': results['value_perception_score']
        })
    
    return validation_results
```

3. [ ] **Step 3: Collect performance data**
```python
def collect_performance_data():
    data_collection = {
        'battery_life': [],
        'data_accuracy': [],
        'user_experience': [],
        'maintenance_requirements': [],
        'cost_effectiveness': []
    }
    
    # Run 100+ hours of continuous testing
    for hour in range(100):
        data_collection['battery_life'].append(measure_battery_life())
        data_collection['data_accuracy'].append(measure_data_accuracy())
        data_collection['user_experience'].append(collect_user_feedback())
        data_collection['maintenance_requirements'].append(assess_maintenance())
        data_collection['cost_effectiveness'].append(calculate_roi())
    
    return data_collection
```

4. [ ] **Step 4: Document results and iterate**
```bash
git add prototype/mvp_prototype.py tests/mvp_validation.py
git commit -m "feat: build and validate MVP prototype"
```

### Task 9: Competitive Intelligence Framework
**Files:**
- `competitive/intelligence_dashboard.py`
- `docs/market_positioning.md`
- `strategy/competitive_analysis.py`
- `README.md` (updated with competitive analysis)

**Steps:**
1. [ ] **Step 1: Identify and monitor competitors**
```python
COMPETITIVE_LANDSCAPE = {
    'direct_competitors': [
        {
            'name': 'Competitor A',
            'technology': 'Traditional soil sensors',
            'strengths': ['established_market', 'brand_recognition'],
            'weaknesses': ['battery_issues', 'limited_features'],
            'market_share': 0.35
        },
        {
            'name': 'Competitor B',
            'technology': 'Alternative bio-batteries',
            'strengths': ['innovation', 'patent_portfolio'],
            'weaknesses': ['scalability', 'cost'],
            'market_share': 0.15
        }
    ],
    'indirect_competitors': [
        {
            'name': 'Traditional sensors',
            'technology': 'Capacitive sensors',
            'strengths': ['mature_technology', 'low_cost'],
            'weaknesses': ['battery_life', 'limited_features'],
            'market_share': 0.50
        }
    ]
}
```

2. [ ] **Step 2: Analyze competitive positioning**
```python
def analyze_competitive_positioning():
    positioning_analysis = {
        'differentiation_factors': [
            'biodegradable_battery_technology',
            '3-year_warranty',
            'lifetime_technical_support',
            'data_analytics_platform'
        ],
        'value_proposition': {
            'target_customers': ['research_labs', 'universities', 'farmers'],
            'key_benefits': ['accuracy', 'reliability', 'cost_effectiveness'],
            'unique_selling_points': [
                'First biodegradable fungal battery',
                '300% longer battery life',
                'Lifetime technical support'
            ]
        },
        'pricing_strategy': {
            'premium_position': 35,
            'value_position': 25,
            'budget_position': 15,
            'market_segments': ['research_labs', 'universities', 'farmers']
        }
    }
    return positioning_analysis
```

3. [ ] **Step 3: Create monitoring dashboard**
```python
class CompetitiveIntelligenceDashboard:
    def __init__(self):
        self.competitor_data = {}
        self.market_trends = {}
        self.customer_sentiment = {}
    
    def update_data(self):
        self.update_competitor_data()
        self.update_market_trends()
        self.update_customer_sentiment()
    
    def get_insights(self):
        insights = []
        insights.extend(self.analyze_competitor_strengths_weaknesses())
        insights.extend(self.analyze_market_trends())
        insights.extend(self.analyze_customer_sentiment())
        return insights
```

4. [ ] **Step 4: Document positioning strategy**
```bash
git add competitive/intelligence_dashboard.py docs/market_positioning.md
git commit -m "feat: implement competitive intelligence framework"
```

---

## Project Timeline & Milestones

```markdown
## Project Timeline

### Phase 1: Technical Validation & Risk Mitigation (Months 1-3)
- **Month 1-2**: Battery performance validation rig operational
- **Month 2-3**: Component redundancy strategy implemented
- **Month 3**: Pilot production line established and tested
- **Month 3**: Technical validation results documented

### Phase 2: Business Model Refinement (Months 4-6)
- **Month 4-5**: Customer segment strategies developed
- **Month 5-6**: Diversified funding strategy implemented
- **Month 6**: Initial customer validation completed
- **Month 6**: Go-to-market strategy finalized

### Phase 3: Regulatory & IP Protection (Months 7-9)
- **Month 7-8**: Regulatory compliance framework established
- **Month 8-9**: IP protection strategy implemented
- **Month 9**: Initial patent applications filed
- **Month 9**: Regulatory exemption applications submitted

### Phase 4: MVP Validation (Months 10-12)
- **Month 10-11**: MVP prototype built and tested
- **Month 11**: Customer validation results analyzed
- **Month 12**: Final business model validated
- **Month 12**: Project completion and handoff

## Critical Success Metrics

### Technical KPIs
- [ ] Battery performance validation: ±20% of projections
- [ ] Component availability: 95% on-time delivery
- [ ] Manufacturing yield: >90% first-pass yield
- [ ] Prototype testing: >80% functional units

### Business KPIs
- [ ] Customer validation: >70% positive feedback
- [ ] Funding secured: 150% of development costs
- [ ] Regulatory compliance: Full exemption granted
- [ ] IP protection: 3+ patents filed

### Financial KPIs
- [ ] Development cost variance: <15% of budget
- [ ] Time to market: <24 months from start
- [ ] Customer acquisition cost: <$100 per unit
- [ ] Lifetime value per customer: >$500

## Risk Mitigation Checklist

### Technical Risks
- [ ] All critical components have backup suppliers
- [ ] Battery performance validated against projections
- [ ] Manufacturing process tested at scale
- [ ] Prototype functionality validated

### Business Risks
- [ ] Customer segments defined with distinct strategies
- [ ] Funding sources diversified with contingency plans
- [ ] Go-to-market strategy tested with target customers
- [ ] Competitive positioning established

### Regulatory Risks
- [ ] EU Battery Regulation compliance strategy developed
- [ ] IP protection strategy implemented
- [ ] Exemption applications submitted
- [ ] Documentation requirements met

## Immediate Action Items (Next 30 Days)

1. **Establish validation protocols** for battery performance testing
2. **Research component alternatives** and backup suppliers
3. **Develop customer segment profiles** and initial outreach plan
4. **Create funding contingency timeline** and backup sources
5. **Initiate regulatory research** and compliance requirements analysis

## Success Criteria

### Phase 1 Success
- Battery performance within 20% of projections
- Component redundancy strategy implemented
- Pilot production yields >90%
- Risk assessment completed

### Phase 2 Success
- Customer segments validated with positive feedback
- Funding strategy secured with contingency plans
- Go-to-market strategy tested and refined
- Market positioning established

### Phase 3 Success
- Regulatory compliance framework operational
- IP protection strategy implemented
- Patent applications filed
- Exemption applications submitted

### Phase 4 Success
- MVP prototype functional and validated
- Customer validation results positive
- Business model validated with real data
- Project ready for commercialization
```
