tobias-weiss-ai-xr/mykovolt/MykoVolt_MAFEX_Anfrage.md

# E-Mail-Entwurf: Anfrage MAFEX-Testkooperation MykoVolt

---

**Betreff:** MykoVolt – Pilz-Brennstoffzelle für Bodensensorik – außerhalb der Wertung?

**An:** Herr Rötz

---

Sehr geehrter Herr Rötz,

ich möchte mit **contextual-intelligence.org** am kommenden Wettbewerb an den Start gehen.

Parallel dazu habe ich im Rahmen des StartMiUp-Businessplan-Wettbewerbs eine Geschäftsmodellskizze für **MykoVolt** entwickelt — eine 3D-gedruckte Pilz-Brennstoffzelle für temporäre Bodensensor-Netzwerke. Da das Thema inhaltlich zur Wettbewerbsrichtung passen könnte, aber nicht mein Hauptbeitrag ist, würde ich es gern **außerhalb der Wertung** einbringen. Die Entwicklung erfolgt nebenberuflich, daher wäre eine anschlussfähige Förderperspektive (EXIST, MAFEX-begleitend) ein wichtiger Faktor, um das Thema über die Konzeptphase hinauszutragen.

Kurz zur Technologie: MykoVolt nutzt lebende Weißfäule-Pilze (*Phanerochaete chrysosporium*) in einer Cellulose-basierten Drucktinte als Biokatalysator. Die Zelle ist trocken lagerbar, vor Ort aktivierbar und nach Gebrauch biologisch abbaubar. Zielanwendung sind Saison-Monitoring und Ad-hoc-Messungen in der Land- und Forstwirtschaft, bei denen Rückholung konventioneller Knopfzellen unwirtschaftlich ist.

**Einordnung in die Marburger Forschungslandschaft:** SYNMIKRO (Zentrum für Synthetische Mikrobiologie) arbeitet hoch relevant — aber an synthetischer Mikrobiologie für Bioproduktion (Chemikalien, Medikamente, CO₂-Verwertung), nicht an mikrobiellen Brennstoffzellen oder Pilz-Batterien. MykoVolt wäre in Marburg kein Duplikat, sondern Neuland. Gleichzeitig hat SYNMIKRO genau die Pilzbiologie-Expertise (Myzel-Kultivierung, Stammcharakterisierung, Fermentation), die für den PoC wertvoll wäre. Eine Kooperation wäre also komplementär.

Wir befinden uns in der **Konzeptphase (TRL 2)** und möchten einen ersten Proof-of-Concept umsetzen (Stamm-Kultivierung, Tintenformulierung, 3D-Druck, elektrochemische Messung). Dafür suchen wir Partner für Laborzugang und biowissenschaftliche Begleitung.

**Meine Frage:** Wäre MAFEX ein geeigneter Rahmen, um einen Test gemeinsam zu starten — etwa als außer Konkurrenz laufendes Projekt oder als studienbegleitende Initiative? Konkret stellen wir uns vor:

1. Nutzung von Laborkapazitäten für Pilzkultur und Tintenentwicklung
2. Einbindung von **Bio-Professuren** (Mykologie/Mikrobiologie/Materialwissenschaft) zur fachlichen Begleitung
3. Beteiligung von **Studierenden** im Rahmen von Praktika, Bachelor-/Masterarbeiten oder einem studentischen Projekt
4. Gemeinsame EXIST-Förderperspektive ab Herbst 2026 für den Fall, dass sich das Thema weiter trägt

Die notwendigen Mittel sind überschaubar (erster PoC ~5 k€ für Verbrauchsmaterial, Stammkultur und Druckmaterial) — das meiste Equipment (3D-Drucker, Potentiostat) ist an der Universität vorhanden.

Könnten wir in den nächsten zwei Wochen einmal kurz telefonieren oder vorbeikommen? Ich würde die Idee gern persönlich vorstellen und Möglichkeiten einer Zusammenarbeit skizzieren.

Beste Grüße

Tobias Weiß
contextual-intelligence.org
0177 9132333

---

## Anlage

- `MykoVolt_Geschaeftsmodellskizze.pdf` (2 S., Business Model Canvas)
- `MykoVolt_PoC.md` (PoC-Plan mit Zeitplan und Budget)

---

## Checklist vor Versand

- [ ] Persönliche Anrede prüfen (ggf. Titel: Prof. Dr. / Dr. Rötz?)
- [ ] Anlagen tatsächlich anhängen (MykoVolt_Geschaeftsmodellskizze.pdf + MykoVolt_PoC.md)
- [ ] Absender-E-Mail-Adresse ergänzen (oberhalb von "Beste Grüße")
- [ ] ggf. Unterschrift digital oder handschriftlich
