tobias-weiss-ai-xr/mykovolt/docs/strategy/PARADIGM.md

# MykoVolt Paradigm

> **"We don't compete. We enable."**

---

## 30 The Core Paradigm

### **Open Research as Competitive Advantage**

At MykoVolt, we operate on a **radically different paradigm** from traditional technology companies:

| Traditional Companies | MykoVolt |
|---|---|
| Hoard knowledge | **Publish all knowledge** |
| Compete with others | **Collaborate with everyone** |
| Create scarcity | **Create abundance** |
| Win-lose | **Win-win-win** |
| Defensive secrecy | **Confident openness** |

**Our belief:** In the age of information abundance, the real competitive advantage is not what you know, but **how fast the ecosystem grows around you**.

---

## 30 The Three Pillars

### **Pillar 1: Open Knowledgebase**
> **"All research, all the time, for everyone."**

**What it means:**
- We publish **100% of our curated research** (90+ papers and growing)
- We structure, analyze, and cross-reference every relevant paper
- We make it **freely available** to researchers, startups, and industry
- We become the **standard reference** for fungal bioelectrochemistry

**Why it works:**
- Researchers cite us as the authoritative source
- Startups build on our foundations instead of reinventing the wheel
- Industry partners come to us for expertise
- We **set the standard** — and everyone references us

**The insight:** The more people use our knowledge, the more valuable we become.

---

### **Pillar 2: Agentic Harness (Proprietary)**
> **"The tools that make the knowledge actionable."**

**What it means:**
- We develop **KI-powered optimization tools** that accelerate R&D
- Bayesian Optimization for strain selection and formulation
- 5-10x faster development than traditional methods
- **Enterprise-only** access (our revenue generator)

**Why it works:**
- The knowledge is open, but **the tools to apply it are proprietary**
- We monetize the **value-add**, not the knowledge itself
- The more people use our open knowledge, the more they want our tools
- **Network effects:** More data → better AI → better tools

**The insight:** Knowledge creates demand for tools. Tools create revenue to fund more open knowledge.

---

### **Pillar 3: Hardware Platform**
> **"The physical manifestation of our knowledge."**

**What it means:**
- NFC DevKit (€35) — Evaluation platform for researchers
- Fungal Pellets (€0.45) — Consumable refills
- End Products (€0.80-2.50) — Complete sensor solutions
- **Razor & Blades 2.0** — Recurring revenue model

**Why it works:**
- Researchers use DevKits to validate our open research
- Industry deploys our hardware with confidence (it's based on open, validated knowledge)
- **Hardware sales fund open research** — virtuous cycle

**The insight:** Open knowledge drives hardware adoption. Hardware sales fund more open knowledge.

---

## 30 The Win-Win-Win Ecosystem

### **For Researchers**
```
✅ Free access to 90+ structured papers
✅ Build on our work — no need to reinvent
✅ Publish with us — co-author opportunities  
✅ Cite MykoVolt as the standard reference
→ Result: Faster research, more citations
```

### **For Startups**
```
✅ Free knowledge base to accelerate R&D
✅ No competition — we're on the same team
✅ Collaboration opportunities with us
✅ Access to our DevKits at cost
→ Result: Faster time-to-market, lower costs
```

### **For Industry**
```
✅ EU-compliant solutions ready to deploy
✅ Pilot programs with our DevKits
✅ Custom development based on open research
✅ First-mover advantage in their sector
→ Result: Compliance achieved, competitive edge gained
```

### **For Investors**
```
✅ Network effects — ecosystem growth = value growth
✅ Platform play — not just a hardware company
✅ Standard-setter — everyone references MykoVolt
✅ 10x potential through ecosystem leverage
→ Result: High-growth, defensible investment
```

### **For MykoVolt**
```
✅ Standard reference in the field
✅ Central node in the ecosystem
✅ Multiple revenue streams (hardware, consumables, tools)
✅ Network effects that compound over time
→ Result: Sustainable, growing, defensible business
```

---

## 30 The Network Effect Flywheel

```
          OPEN RESEARCH (90+ Papers)
                ↓
    Researchers cite MykoVolt as standard
                ↓
    MykoVolt becomes De-facto Authority
                ↓
    Startups build on MykoVolt foundations
                ↓
    Industry adopts MykoVolt solutions
                ↓
    Ecosystem grows exponentially
                ↓
    More data from ecosystem → Better AI (Agentic Harness)
                ↓
    MykoVolt tools become more valuable
                ↓
    Revenue from tools funds more open research
                ↓
    OPEN RESEARCH (100+ Papers, better structured)
                ↓
    [Flywheel accelerates]
```

**The paradox:** The more we give away, the more valuable we become.

---

## 30 Strategic Principles

### **Principle 1: Openness is Our Moat**
> **"In the knowledge economy, secrecy is the fastest path to irrelevance."**

- We publish **all non-proprietary research** immediately
- We structure data in **machine-readable formats**
- We encourage **third-party contributions**
- We maintain **academic rigor** in all publications

### **Principle 2: Collaboration > Competition**
> **"A rising tide lifts all boats, and we want to be the tide."**

- We **partner** rather than compete
- We **enable** rather than block
- We **share** rather than hoard
- We **lead** rather than follow

### **Principle 3: Knowledge is Free, Tools are Valuable**
> **"Give away the knowledge, sell the implementation."**

- **Open:** Research, data, insights, standards
- **Proprietary:** AI tools, optimization algorithms, enterprise APIs
- **Monetization:** Hardware, consumables, enterprise tools

### **Principle 4: Standard-Setter > Market-Share-Taker**
> **"It's better to own 10% of a huge ecosystem than 100% of a tiny one."**

- We aim to be **the standard** in fungal bioelectrochemistry
- We want everyone to **reference MykoVolt** in their work
- We measure success by **ecosystem growth**, not just revenue

### **Principle 5: Network Effects Compound**
> **"Every new participant makes the whole ecosystem more valuable."**

- More researchers → more citations → more authority
- More startups → more applications → more adoption
- More industry partners → more revenue → more investment in R&D
- **Result:** Exponential growth of the entire ecosystem

---

## 30 The Business Model

### **Revenue Streams (2030 Projection: €91.4M)**

| Stream | Contribution | Products | Margin | Defensibility |
|---|---|---|---|---|
| **Hardware** | 40% | DevKits, End Products | 50-60% | Manufacturing excellence |
| **Consumables** | 30% | Fungal Pellets, Refills | 75% | Recurring, proprietary formulation |
| **Platform** | 30% | Agentic Harness, Enterprise API | 80% | Network effects, AI superiority |

### **Reinvestment Strategy**

```
Hardware Profits → Fund open research
Consumable Profits → Improve manufacturing
Platform Profits → Enhance AI tools

All profits → Grow the ecosystem → Increase all revenue streams
```

**The cycle is self-reinforcing.**

---

## 30 The Competitive Landscape

### **Direct Competitors**
> **"There are none — because we've redefined competition."**

Traditional competitors would:
- Hoard their research (slows them down)
- Compete with everyone (makes enemies)
- Try to own the whole stack (limits growth)

**MykoVolt does the opposite:**
- We publish all research (accelerates everyone, including us)
- We collaborate with everyone (makes allies)
- We enable the ecosystem (expands the market)

**Result:** Traditional competitors can't keep up because they're playing a different game.

### **Potential "Competitors" (Actually Partners)**

| Company Type | Traditional Approach | MykoVolt Approach |
|---|---|---|
| **Research Institute** | Keep findings secret | Publish with us, cite us |
| **Battery Startup** | Reinvent the wheel | Build on our open knowledge |
| **Material Supplier** | Sell to highest bidder | Collaborate on open standards |
| **Sensor Company** | Develop proprietary tech | Use our EU-compliant solutions |

**We don't have competitors. We have an ecosystem.**

---

## 30 Implementation Guidelines

### **What We Always Do**
- ✅ Publish research **openly and immediately**
- ✅ Structure data for **machine-readability**
- ✅ Cite **all sources** transparently
- ✅ Encourage **third-party contributions**
- ✅ Maintain **academic rigor**
- ✅ Share **insights freely**

### **What We Never Do**
- ❌ Hoard knowledge for competitive advantage
- ❌ Create artificial scarcity
- ❌ Obstruct third-party research
- ❌ Claim exclusive rights to open knowledge
- ❌ compete with our ecosystem partners

### **What We Monetize**
- 💰 **Hardware** (physical products)
- 💰 **Consumables** (recurring sales)
- 💰 **Enterprise Tools** (Agentic Harness, APIs)
- 💰 **Custom Development** (industry-specific solutions)

### **What We Give Away**
- 🎁 **Research papers** (structured, cross-referenced)
- 🎁 **Knowledge base** (searchable, queryable)
- 🎁 **Standards & protocols** (open, extensible)
- 🎁 **Basic tools** (for researchers, startups)

---

## 30 Success Metrics

### **Ecosystem Metrics**
| Metric | Target 2026 | Target 2027 | Target 2030 |
|---|---|---|---|
| Papers in Knowledgebase | 90 | 200+ | 500+ |
| Researchers citing MykoVolt | 50 | 500+ | 5000+ |
| Startups in ecosystem | 10 | 100+ | 1000+ |
| Industry partners | 5 | 50+ | 500+ |
| GitHub stars (research repo) | 100 | 1000+ | 10,000+ |

### **Business Metrics**
| Metric | Target 2026 | Target 2027 | Target 2030 |
|---|---|---|---|
| Revenue | €175K | €1.875M | €91.4M |
| DevKits sold | 100 | 10,000+ | 100,000+ |
| Pellet production | 1K/day | 10K/day | 100K/day |
| Platform revenue | €0 | €250K | €27.4M |
| Valuation | €2.5M | €18M | €550M |

### **Paradigm Metrics**
| Metric | Measurement |
|---|---|
| **Standard-setter** | % of fungal MFC papers citing MykoVolt |
| **Ecosystem enabler** | # of startups using our open research |
| **Collaboration success** | # of joint publications/partnerships |
| **Network effects** | Growth rate of ecosystem vs. our revenue |

---

## 30 The Long-Term Vision

### **2026: Foundation**
- Publish 90+ papers openly
- Launch DevKit v0.1
- Establish knowledgebase as reference
- First ecosystem partnerships
- **SOHO Lab experiments**: validate papers with Pi 5 + Hailo + 3D printers → first open datasets ([SOHO Lab Pipeline](../projects/SOHO_LAB_PIPELINE.md))

### **2027: Acceleration**
- 200+ papers in knowledgebase
- Agentic Harness v1.0 (Enterprise)
- 100+ DevKits in the wild
- First industry pilots
- **SOHO Lab products**: Portable MFC Charger (€99), DevKit v0.2 with Pi 5 integration, Autonomous Fungal Farm

### **2028: Standardization**
- MykoVolt = De-facto standard in fungal bioelectrochemistry
- First CE-certified biodegradable battery
- 1000+ researchers using our knowledgebase
- €13.76M revenue

### **2030: Ecosystem Domination**
- **The Wikipedia of Fungal Bio-Elektrochemie**
- 500+ papers in knowledgebase
- 5000+ researchers citing MykoVolt annually
- 1000+ startups in the ecosystem
- €91.4M revenue
- €550M valuation

### **2035: World Standard**
- **Every fungal MFC application references MykoVolt**
- Open research is the industry norm (because we proved it works)
- MykoVolt tools are the gold standard for R&D
- Biodegradable batteries are mandatory (and MykoVolt is the leader)

---

## 30 The Paradigm in One Sentence

> **"By making our knowledge free, we make ourselves indispensable."**

---

## 30 Key Takeaways

1. **Openness is our moat** — The more we share, the more valuable we become
2. **Collaboration is our strategy** — We enable others to succeed, which makes us succeed
3. **Knowledge is free, tools are valuable** — We give away the knowledge, sell the implementation
4. **Standard-setter > Market-share-taker** — We'd rather own 10% of a huge ecosystem than 100% of a tiny one
5. **Network effects compound** — Every new participant makes the whole ecosystem more valuable

**This is not just a business strategy. It's a paradigm shift for how technology companies should operate in the 21st century.**

---

## SOHO Lab Integration

The [SOHO Lab Pipeline](../projects/SOHO_LAB_PIPELINE.md) operationalizes this paradigm using accessible hardware:

| Hardware | Role | Pillar |
|---|---|---|
| Pi 5 + Hailo-8 | Edge AI inference, data collection | Knowledgebase + Harness |
| Anycubic Kobra S1 | MFC prototypes, robot parts | Hardware Platform |
| Ender 3 (print + laser) | PCB prototyping, enclosures | Hardware Platform |

**15 projects** across 3 phases, each producing open data that feeds the flywheel:
```
SOHO Experiments → Open Datasets → Researchers Cite Us → Ecosystem Grows → More Experiments
```

This is the paradigm in action: **every experiment makes the knowledgebase more valuable, which makes MykoVolt more indispensable.**

---

## 30 Document Information

| Field | Value |
|---|---|
| **Version** | 1.0 |
| **Created** | August 2026 |
| **Author** | MykoVolt Team |
| **Status** | Active Paradigm |
| **Next Review** | Q1 2027 |
| **Location** | `/docs/strategy/PARADIGM.md` |

---

> **"The best way to predict the future is to create it — and the best way to create it is to enable others to create it with you."**

> — MykoVolt Team, August 2026
