tobias-weiss-ai-xr/mykovolt/research/docs/research/trends.md

# Trends (12-Month View)

**Generated:** 2026-09-02  
**Window:** since 2025-09 — 14 of 125 papers

## 🔥 Keyword Bursts

| Keyword | Recent | Total | Burst |
|---|---|---|---|
| policy | 1 | 1 | 8.9× |
| decision | 1 | 1 | 8.9× |
| uncertainty | 1 | 1 | 8.9× |
| causal | 1 | 1 | 8.9× |
| human | 2 | 4 | 4.5× |
| tool | 2 | 4 | 4.5× |
| learning | 1 | 2 | 4.5× |
| generate | 2 | 6 | 3.0× |
| graph | 2 | 8 | 2.2× |
| imitation | 1 | 4 | 2.2× |
| transfer | 1 | 15 | 0.6× |

## 📈 Fastest-Growing Cells

| Cell | Recent | Total | Recent Share |
|---|---|---|---|
| `application/degradation` | 1 | 1 | 100% |
| `mechanism/eet` | 8 | 12 | 67% |
| `mechanism/degradation` | 2 | 16 | 12% |
| `material/degradation` | 1 | 10 | 10% |
| `material/laccase` | 1 | 15 | 7% |
| `application/hybrid` | 1 | 30 | 3% |

Regenerate with `python3 tools/trend_scanner.py --months 12`.
