tobias-weiss-ai-xr/mykovolt/archive/archive_MykoVolt_1Pager_EMC.md

> ⚠️ ARCHIVE — Historical one-pager. Timeline and pricing updated to reflect current TRL-2 assessment.

# MykoVolt — One-Pager

**Mutterunternehmen:** contextual-intelligence.org | **Gründer:** Tobias Weiß | **Stand:** Juni 2026

---

## Problem

Präzisionslandwirtschaft benötigt hochaufgelöste Bodendaten aus Tausenden Sensoren. Die Rückholung konventioneller Batterie-Sensoren ist unwirtschaftlich, Recyclingquoten liegen unter 5 %. Es existiert kein kommerzieller Ansatz, der biologisch abbaubare Stromquellen mit akzeptabler Leistungsdichte kombiniert.

---

## Lösung

MykoVolt entwickelt mikrobielle Brennstoffzellen auf Basis lebender Pilze in cellulosehaltiger Tinte. Die Zellen sind trocken lagerbar, vor Ort mit Wasser und Zucker aktivierbar und vollständig kompostierbar. Maschinelles Lernen beschleunigt die Stammselektion und Tintenoptimierung — R&D erfolgt datengetrieben statt per Trial-and-Error.

---

## Technologie

| Parameter | Wert |
|---|---|
| Empa-Baseline (Reyes et al., 2024) | 12,5 µW/cm² |
| KI-Simulationsoptimum (Bayesian Optimization) | 261 µW/cm² (Simulationsziel, experimentell unbestätigt) |
| E2E-Sensor-Tag | 7 Tage Betriebszeit @ ca. EUR 0,15 |
| Gehäuse | Cellulose + Bienenwachs — biologisch abbaubar |
| Formgebung R&D | 3D-Druck (DIW); Scale-Up: Pressling/Filmgießen |

Die KI-Simulation identifiziert den ohmschen Widerstand der Tinte als dominierenden Flaschenhals, nicht die Enzymaktivität.

---

## Markt

- **TAM Bio-Batterien:** USD 96,1 Mrd. (2024), CAGR 8,2 % bis 2035 (Roots Analysis)
- **Nische:** Kompostierbare Bodensensoren für AgrarTech, Bio-Betriebe und Umweltbehörden
- **Wettbewerbsvorteil:** Kein Akteur kombiniert Biologische Abbaubarkeit, ML-gesteuerte FuE und kostengünstige Massenfertigung
- **Erstes Produkt:** Bodenfeuchte-Sensor-Tag — keine regulatorischen Hürden, schnellster Weg zum zahlenden Kunden

---

## Aktueller Stand

- **TRL 2** — Technisches Konzept mit experimenteller Validierung (Empa) und KI-gestützter Simulation
- **Simulationsergebnisse** bestätigen Machbarkeit eines E2E-Sensor-Tags bei optimierter Tintenformulierung
- **Richtungswissen:** Stammtransfer (hochleistungsfähige Pilze) in druckbares Design ist Kerninnovation, noch ungelöst

---

## Team

- **Tobias Weiß** — Gründer, contextual-intelligence.org; Hintergrund in ML/AI und datengetriebener Forschung
- **Geplante Kooperationen:** SYNMIKRO Marburg (Pilzbiologie), Fachbereich KI/Informatik Uni Marburg (ML-Pipeline)
- Teamziel: Biotech, ML/Data Science, Materials Science (3 Kernpersonen)

---

## Roadmap

| Phase | Zeitraum | Meilenstein |
|---|---|---|
| Lab-Validierung | Jahr 1–3 | Tinten-Optimierung, Stamm-Screening via ML, Prototyp > 50 µW/cm² |
| Feldtests | Jahr 3–5 | Pilotprojekte mit Agrarbetrieben, Bodenfeuchte-Tag |
| Markteintritt | Jahr 5–7 | Developer Kit (EUR 24–35), OEM-Komponente (Ziel EUR 3–5) |

---

## Was wir suchen

- Zugang zu Biotech-Laborinfrastruktur (SYNMIKRO oder vergleichbar)
- Beratung zu Fördermitteln (EXIST, BMBF, Horizon Europe)
- Netzwerk zu Agrarbetrieben und Umweltbehörden für Pilotprojekte
