tobias-weiss-ai-xr/mykovolt/archive/archive_MykoVolt_Geschaeftsmodellskizze.md

# Geschäftsmodellskizze — StartMiUp Business Model Wettbewerb 2026

> ⚠️ ARCHIVE — Wettbewerbseinreichung Juni 2026. Preis- und Zeitplanangaben wurden auf TRL-2-Baseline aktualisiert. Siehe MykoVolt-mvp-design.md für aktuelle Planung.

> **Format:** Arial 11 pt, 1,5-zeilig, Seitenränder Standard | **Einreichung als PDF**
>
> **Hinweis zur Formatierung:** Dieses Markdown als PDF exportieren. Zeichenzählungen beziehen sich auf den jeweiligen Inhaltsabschnitt zwischen den Trennlinien.

---

## 1. Einleitung

MykoVolt entwickelt 3D-gedruckte Pilz-Brennstoffzellen für Bodensensoren. Problem: Saison-Monitoring tausender Sensoren — Rückholung unwirtschaftlich, Batteriemüll. MykoVolt nutzt Weißfäulepilze als Biokatalysator in Cellulose-Tinte. KI (ML-Stammoptimierung, Data-Driven Tintendesign) beschleunigt FuE und macht Stammtransfer vorhersagbar.

---

**Zeichenzahl Abschnitt 1:** ~339 Zeichen ✓

---

## 2. Wertangebot / Value Proposition

**Zielgruppe:** AgrarTech-Dienstleister, Bio-Betriebe (fungizidfrei); Forst-/Umweltbehörden; Forschung.

**Problem:** Präzise Landwirtschaft braucht hochaufgelöste Bodendaten — Sensornetzwerke hinterlassen Batteriemüll. Rückholung unwirtschaftlich, Recyclingquoten unter 5 %. Reyes et al. (Empa 2024) zeigen Pilz-MFC im Lab — Transfer leistungsfähiger Stämme ins 3D-Druck-Design ist ungelöst.

**USP:** (1) Pilz-MFC aus Cellulose, Biochar, Carnaubawachs — trocken lagerbar (≥6 Mte.), biologisch abbaubar. (2) ML-gestützte FuE: Data-Driven statt Trial-and-Error — ML für Stamm-Screening, Tintenoptimierung und Prozess-Monitoring. (3) Kooperation SYNMIKRO + Uni KI. Developer Kit; ab J3 OEM.

---

**Zeichenzahl Abschnitt 2:** ~689 Zeichen ✓

---

## 3. Geschäftsmodell-Logik / Business Model Canvas

**Kundensegmente:** (a) AgrarTech-Dienstleister + Bio-Betriebe (fungizidfrei); (b) Forst-/Umweltbehörden (Schutzgebiete, Katastrophen); (c) Forschungsinstitute (J3).

**Kanäle:** B2B-Pilotprojekte mit Agrarverbünden. Konferenzen (Agritechnica, Sensor+Test). Kooperation Uni Marburg (SYNMIKRO + FB KI) für Wissenschafts-Publikationen und FuE-Credibility.

**Kundenbeziehungen:** Co-Development mit Pilotkunden. Technischer Support für Integration. Betriebsdauer Tage–Wochen pro Sensor — gesamte Einheit wird getauscht.

**Einnahmen:** (1) Developer Kit 24–35 € (Zelle + Board); (2) OEM-Komponente ab J3 (Ziel 3–5 €); (3) Forschungsförderung (EXIST, BMBF); (4) Forschungsdaten-Sets (Tintenperformance, Stammcharakteristik) für ML-Gemeinschaft.

**Schlüsselressourcen:** Bio-Lab (SYNMIKRO Marburg), KI-Infrastruktur (GPU-Cluster für Tinten-ML-Optimierung), 3D-Drucker, elektrochemisches Equipment. IP: Tinten + Stamm + Druckprozess + ML-Modelle für FuE.

**Schlüsselaktivitäten:** (a) Stamm-Screening via ML (billionen Kombinationen → Top-Kandidaten); (b) Tintenformulierung (Data-Driven); (c) ML-basiertes Prozess-Monitoring (Zellviabilität, Leistungsvorhersage); (d) Feldtests; (e) IP-Aufbau.

**Schlüsselpartner:** (1) SYNMIKRO Marburg (Pilzbiologie, Myzel-Kultivierung); (2) Uni Marburg FB KI/Informatik (ML-Pipeline, Data-Driven Biology); (3) Agrar-Versuchsstationen (Feldzugang); (4) Holz-/Pyrolyse-Betriebe.

**Wettbewerber:** BeFC (enzymatische Papier-Batterie), Bactery AB (bakterielle MFC), MycelioTronics (Myzel-Separator). Substitute: Solar-Bodensensoren. Alle Wettbewerber optimieren Tinten manuell — MykoVolt nutzt ML, um schneller und zielgerichteter zu entwickeln.

**Kostenstruktur:** Personal: Biotech, ML/Datascience, MatSci (80–150 k€/J). Labormaterial ~2–4 €/Zelle. KI-Infrastruktur: GPU-Cluster für Training (Uni). 3D-Druck Prototypen; Skalierung via Siebdruck. Zell-Ziel: 3–5 €.

---

**Zeichenzahl Abschnitt 3:** ~1898 Zeichen ✓

---

## 4. Kreativität & Umsetzbarkeit

**Innovationsgrad:** Erste Pilz-MFC in 3D-druckbarer Cellulosetinte mit ML-FuE. Basis: Reyes (12,5 µW/cm²), Sukri (1,9 W/m²). 5–15× anvisiert. KI: ML-Stamm-Screening + Data-Driven Tintendesign statt trial-and-error.

**Umsetzbarkeit:** Risiken: (1) Bakterien-Konkurrenz; (2) Pilz 10–30 °C; (3) Scherstress Druck; (4) µW-Limit. Kill J1: >50 µW/cm²/14 d + ML-Pipeline. TRL 2→7, 5–7 J. Team: 3 (Biotech, ML, MatSci). Koop: SYNMIKRO + Uni KI.

---

**Zeichenzahl Abschnitt 4:** ~438 Zeichen ✓

---

## Checklist vor Einreichung

- [ ] Markdown → PDF konvertieren (Arial 11pt, 1,5-zeilig)
- [ ] Zeichenzahl final prüfen (in Word/LibreOffice: Zeichen inkl. Leerzeichen)
- [ ] Team-Mitglieder berechtigt? (Student:in/Mitarbeiter:in/Alumni JLU Gießen, Uni Marburg, THM — bis 5 Jahre nach Abschluss)
- [ ] Beitrag ist Originalarbeit, verletzt keine Rechte Dritter — **Hinweis:** Empa-Patente nicht verletzt, da MykoVolt auf eigenständiger Stammentwicklung und Tintenformulierung basiert
- [ ] Vorgründungsphase: keine Kapitalgesellschaft gegründet, kein Umsatz
- [ ] Pretix-Abfrage ausfüllen: [pretix.eu/startmiup/BMwettbewerb26/](https://pretix.eu/startmiup/BMwettbewerb26/)
- [ ] Einreichfrist: **26.06.2026, 23:59 Uhr**
- [ ] Finalist:innen-Videotermin freihalten: 16./17./20./21.07.2026
- [ ] Kontakt: Matthias Beurer — info@startmiup.de
