tobias-weiss-ai-xr/mykovolt/simulation/optimization_history.png

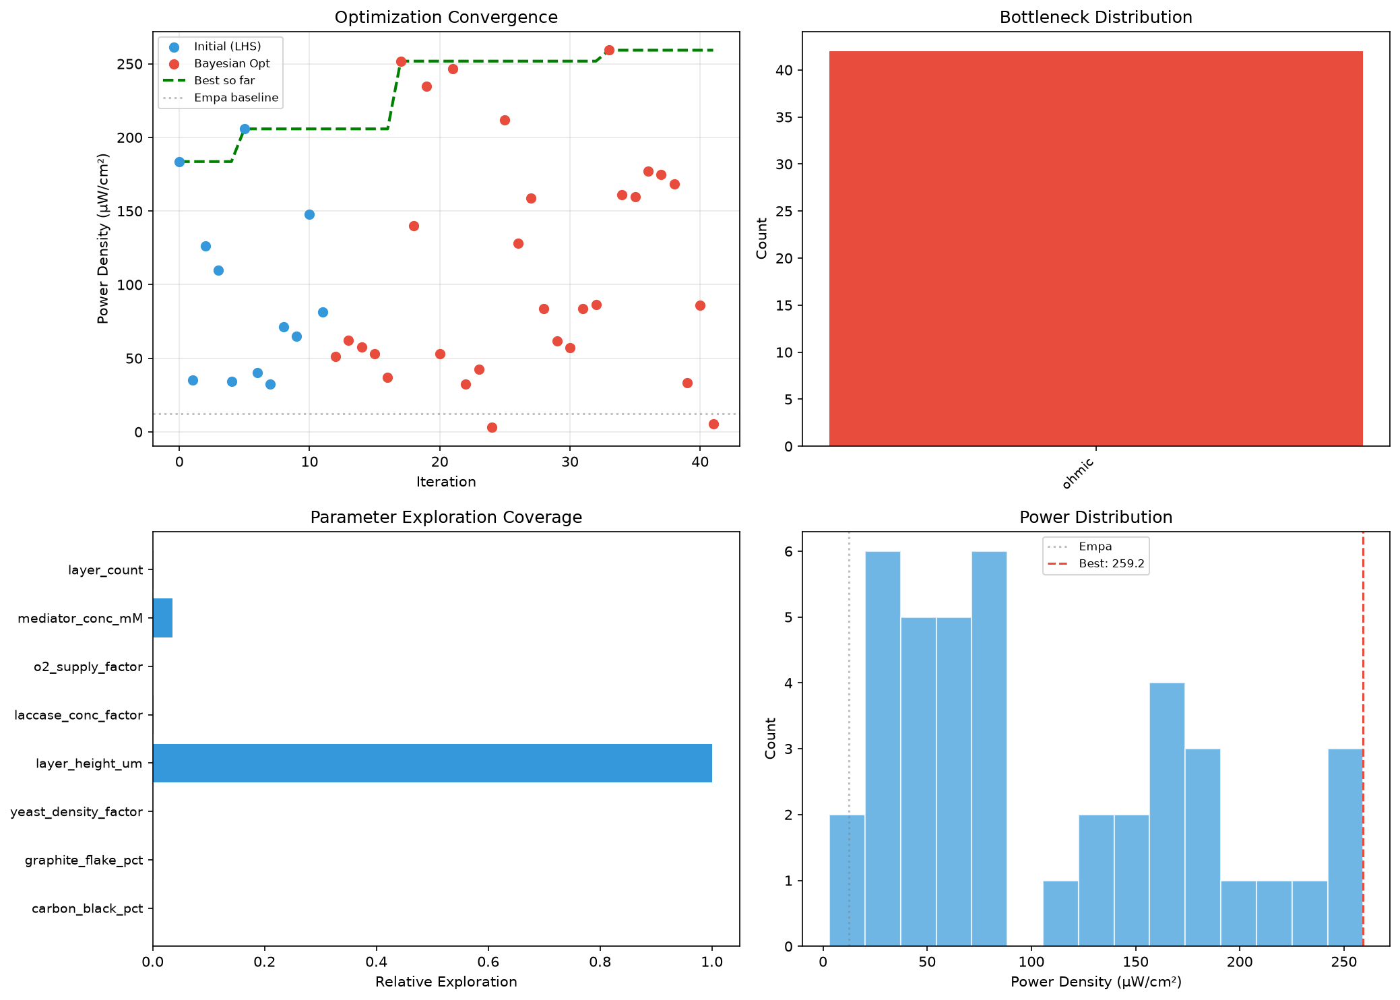
simulation/optimization_history.png
