tobias-weiss-ai-xr/mykovolt/hardware/kicad/mykovolt_devkit.kicad_sch

## KiCad design hardware/kicad/mykovolt_devkit.kicad_sch (2026-07-29)

Schematic: mykovolt_devkit.kicad_sch

Parts:
C1, C2, C3, C4, C5, C6, C7, C8, C9, C10, C22, C23, C24: 100nF; C_0603_1608Metric
C11, C12, C13: 1µF; C_0603_1608Metric
C14, C15: 10µF; C_0805_2012Metric
C16, C17: 22pF; C_0603_1608Metric
C18, C19: 100pF; C_0603_1608Metric
C20: 47pF; C_0603_1608Metric
C21: 4.7µF; C_0603_1608Metric
D1: USBLC6-2P6; SOT-666
D2: PESD5V0S1UB; D_SOD-523
J1: SWD_2x5; PinHeader_2x05_P1.27mm_Vertical_SMD
J2: Pressling; JST_PH_B2B-PH-K_1x02_P2.00mm_Vertical
J3: Aux_I2C; JST_PH_B2B-PH-K_1x02_P2.00mm_Vertical
J4: Sensor_In; PinHeader_2x03_P1.27mm_Vertical_SMD
L1: 10µH; L_Vishay_IFSC-1515AH_4x4x1.8mm
L2: 47µH; L_Bourns-SRN4018
LED1: Green; LED_0603_1608Metric
LED2: Yellow; LED_0603_1608Metric
Q1: SI1308EDL; SOT-323_SC-70
R1, R2: 2.2kΩ; R_0603_1608Metric
R3, R4: 47kΩ; R_0603_1608Metric
R5, R6: 510kΩ; R_0603_1608Metric
R7, R8: 1MΩ; R_0603_1608Metric
R9: 100kΩ; R_0603_1608Metric
R10: 220kΩ; R_0603_1608Metric
R11: 22Ω; R_0603_1608Metric
R12: 100Ω; R_0603_1608Metric
R13, R14: 330Ω; R_0603_1608Metric
SC1: 100mF; CP_Radial_D8.0mm_P3.50mm
U1: STM32L011F4Px; TSSOP-20_4.4x6.5mm_P0.65mm
U2: BQ25570; QFN-20-1EP_3.5x3.5mm_P0.5mm_EP2x2mm
U3: ST25DV04K; SOIC-8_3.9x4.9mm_P1.27mm
U4: MB85RC16; SOIC-8_3.9x4.9mm_P1.27mm
U5: PCF8523T; SOIC-8_3.9x4.9mm_P1.27mm
U6: FDC1004; Texas_S-PWSON-N10
X1: 32.768kHz; Crystal_SMD_3215-2Pin_3.2x1.5mm
