tobias-weiss-ai-xr/mykovolt/simulation/ai_optimizer.py

#!/usr/bin/env python3
"""
AI-Optimierung der Pilz-Bio-Batterie — Bayesian Optimization Prototype

Architektur:
  [Parameter Space] ─→ [Graph Simulation] ─→ [Power Density]
        ↑                      │
        │                      ↓
  [Bayesian Optimizer] ←─ [GP Surrogate Model]
        │
        ↓
  [Nächste experimentelle Formulierung]

Level 1: Tinten-Formulierung (8 Parameter)
Level 2: GNN auf e⁻-Transport-Graph (nicht-lineare Synergien)
Level 3: RL für 3D-Druck-Geometrie

Dieser Prototype implementiert Level 1+2.
"""

import numpy as np
import matplotlib
matplotlib.use('Agg')
import matplotlib.pyplot as plt
from sklearn.gaussian_process import GaussianProcessRegressor
from sklearn.gaussian_process.kernels import Matern, RBF, WhiteKernel, ConstantKernel
from scipy.optimize import minimize
from scipy.stats import norm
import warnings
warnings.filterwarnings('ignore')

# Re-import the graph simulation
import sys, os
sys.path.insert(0, os.path.dirname(os.path.abspath(__file__)))
from electron_transport_graph import FungalMFCGraph, FARADAY, INTERNAL_RESISTANCE, LOAD_RESISTANCE, \
    YEAST_CELLS, CELL_AREA, GLUCOSE_CONSUMPTION, ABTS_TURNOVER, LACCASE_KCAT_T_PUB, \
    LACCASE_CONC, O2_CONCENTRATION

# =============================================================================
# PARAMETER SPACE
# =============================================================================
# 8 formulation parameters that map to simulation constants

PARAM_NAMES = [
    "carbon_black_pct",       # % w/v in ink (affects conductivity)
    "graphite_flake_pct",     # % w/v in ink (affects conductivity)
    "yeast_density_factor",   # × baseline (1e8 cells)
    "layer_height_um",        # µm (affects roughness)
    "laccase_conc_factor",    # × baseline (10 µM)
    "o2_supply_factor",       # × baseline (air-breathing efficiency)
    "mediator_conc_mM",       # mM (ABTS concentration)
    "layer_count",            # number of printed layers
]

# Bounds: [min, max] for each parameter
PARAM_BOUNDS = np.array([
    [0.5, 15.0],    # carbon_black_pct
    [1.0, 25.0],    # graphite_flake_pct
    [0.1, 5.0],     # yeast_density_factor
    [10.0, 500.0],  # layer_height_um
    [0.1, 20.0],    # laccase_conc_factor
    [0.1, 10.0],    # o2_supply_factor
    [1.0, 100.0],   # mediator_conc_mM
    [1.0, 20.0],    # layer_count
])

# Default (Empa baseline)
PARAM_DEFAULT = np.array([
    [5.0],    # carbon_black_pct
    [10.0],   # graphite_flake_pct  
    [1.0],    # yeast_density_factor
    [100.0],  # layer_height_um
    [1.0],    # laccase_conc_factor
    [1.0],    # o2_supply_factor
    [20.0],   # mediator_conc_mM (Empa: 20 mM)
    [7.0],    # layer_count (Empa: 7 layers)
]).flatten()

# =============================================================================
# EVALUATION FUNCTION - Maps parameters → power density via graph simulation
# =============================================================================

def evaluate_formulation(params, strain="T_pubescens"):
    """
    Given 8 formulation parameters, run the graph simulation and return power density.
    This is the "digital twin" — evaluates in silico before printing.
    """
    p = {name: val for name, val in zip(PARAM_NAMES, params)}
    
    # Map parameters to simulation constants (using globals as a quick approach)
    # In production, this would use a proper config object
    
    # Conductivity: carbon black + graphite contribute
    # Higher % → lower internal resistance
    carbon_effect = p["carbon_black_pct"] / 5.0  # normalized to default
    graphite_effect = p["graphite_flake_pct"] / 10.0
    conductivity_factor = 0.3 * carbon_effect + 0.7 * graphite_effect
    
    # Internal resistance scales inversely with conductivity
    r_internal = INTERNAL_RESISTANCE / max(conductivity_factor, 0.1)
    
    # Effective surface area from layer height + count
    # Thinner layers + more layers = more surface area
    roughness = (p["layer_count"] * p["layer_height_um"] / (7 * 100)) * 50
    roughness = max(roughness, 1.0)
    
    # Yeast: more cells = more glucose consumption
    yeast_eff = YEAST_CELLS * p["yeast_density_factor"]
    
    # Laccase: more enzyme = faster turnover
    laccase_eff = LACCASE_CONC * p["laccase_conc_factor"]
    
    # O₂ supply
    o2_eff = O2_CONCENTRATION * p["o2_supply_factor"]
    
    # Mediator
    mediator_eff = p["mediator_conc_mM"] / 20.0  # normalized to Empa
    
    # Modify globals for simulation
    orig_r = INTERNAL_RESISTANCE
    orig_y = YEAST_CELLS
    orig_lc = LACCASE_CONC
    orig_o2 = O2_CONCENTRATION
    
    import electron_transport_graph as etg
    etg.INTERNAL_RESISTANCE = r_internal
    etg.YEAST_CELLS = yeast_eff
    etg.LACCASE_CONC = laccase_eff
    etg.O2_CONCENTRATION = o2_eff
    etg.ABTS_TURNOVER = ABTS_TURNOVER * max(mediator_eff, 0.1)
    
    # Rebuild graph and evaluate
    try:
        mfc = FungalMFCGraph(strain=strain)
        result = mfc.bottleneck_analysis()
        power = result["max_power_density_uW_cm2"]
        bottleneck = result.get("bottleneck_rate_type", "unknown")
        current = result["max_current_uA"]
    except Exception as e:
        power = 0.0
        bottleneck = str(e)
        current = 0.0
    
    # Restore
    etg.INTERNAL_RESISTANCE = orig_r
    etg.YEAST_CELLS = orig_y
    etg.LACCASE_CONC = orig_lc
    etg.O2_CONCENTRATION = orig_o2
    etg.ABTS_TURNOVER = ABTS_TURNOVER
    
    return power, bottleneck, current, {

    }

# =============================================================================
# GAUSSIAN PROCESS SURROGATE MODEL
# =============================================================================

class FormulationGP:
    """GP that learns the mapping from 8 formulation params to power density."""
    
    def __init__(self):
        kernel = (ConstantKernel(1.0) * 
                  Matern(length_scale=np.ones(8), nu=2.5) + 
                  WhiteKernel(noise_level=0.1))
        self.gp = GaussianProcessRegressor(
            kernel=kernel,
            alpha=1e-6,
            normalize_y=True,
            n_restarts_optimizer=5,
            random_state=42
        )
        self.X = []  # evaluated parameters
        self.y = []  # observed power densities
    
    def add_observation(self, params, power):
        self.X.append(params)
        self.y.append(power)
    
    def fit(self):
        if len(self.X) < 3:
            return
        X = np.array(self.X)
        y = np.array(self.y)
        self.gp.fit(X, y)
    
    def predict(self, X, return_std=True):
        if len(self.X) < 3:
            return np.zeros(len(X)), np.ones(len(X)) * 100
        return self.gp.predict(X, return_std=return_std)

# =============================================================================
# ACQUISITION FUNCTION - Expected Improvement
# =============================================================================

def expected_improvement(X, gp, y_best, xi=0.01):
    """Expected Improvement acquisition function."""
    mu, sigma = gp.predict(X.reshape(1, -1), return_std=True)
    sigma = sigma.ravel()
    
    with np.errstate(divide='warn'):
        imp = mu - y_best - xi
        Z = imp / sigma
        ei = imp * norm.cdf(Z) + sigma * norm.pdf(Z)
        ei[sigma == 0.0] = 0.0
    
    return ei.ravel()

def suggest_next_experiment(gp, bounds, y_best, n_restarts=10):
    """Find the next parameter set that maximizes expected improvement."""
    best_x = None
    best_ei = -np.inf
    
    dim = bounds.shape[0]
    
    for _ in range(n_restarts):
        x0 = np.random.uniform(bounds[:, 0], bounds[:, 1])
        
        def negative_ei(x):
            ei = expected_improvement(x, gp, y_best)
            return -ei[0]
        
        res = minimize(negative_ei, x0, method='L-BFGS-B', 
                       bounds=bounds, options={'maxiter': 200})
        
        if res.fun < -best_ei:
            best_ei = -res.fun
            best_x = res.x
    
    return best_x, best_ei

# =============================================================================
# MAIN OPTIMIZATION LOOP
# =============================================================================

def run_optimization(n_initial=10, n_iterations=40):
    """
    Führt die vollständige Bayesian Optimization durch.
    
    Phase 1: Latin Hypercube Sampling (n_initial random experiments)
    Phase 2: Bayesian Optimization (n_iterations guided by GP)
    """
    
    bounds = PARAM_BOUNDS
    gp = FormulationGP()
    history = []
    dim = bounds.shape[0]
    
    print("=" * 60)
    print("  AI-OPTIMIZATION: FUNGAL BIO-BATTERY FORMULATION")
    print("=" * 60)
    print(f"\n  Parameter Space: {dim} dimensions")
    print(f"  Initial samples: {n_initial}")
    print(f"  BO iterations:  {n_iterations}")
    print(f"  Total budget:   {n_initial + n_iterations} evaluations")
    print()
    
    # ── Phase 1: Latin Hypercube Initialization ──
    print("  PHASE 1: Initial exploration")
    print("  " + "-" * 50)
    
    from scipy.stats import qmc
    sampler = qmc.LatinHypercube(dim, seed=42)
    samples = sampler.random(n=n_initial)
    samples = qmc.scale(samples, bounds[:, 0], bounds[:, 1])
    
    for i, params in enumerate(samples):
        power, bottleneck, current, _ = evaluate_formulation(params)
        gp.add_observation(params, power)
        history.append({
            "iteration": i,
            "phase": "initial",
            "params": params.copy(),
            "power": power,
            "bottleneck": bottleneck,
            "current": current,
        })
        print(f"    [{i+1:2d}/{n_initial}] P = {power:7.2f} µW/cm²  |  "
              f"I = {current:6.1f} µA  |  {bottleneck}")
    
    # Fit initial GP
    gp.fit()
    
    # ── Phase 2: Bayesian Optimization ──
    print(f"\n  PHASE 2: Bayesian Optimization ({n_iterations} iterations)")
    print("  " + "-" * 50)
    
    for it in range(n_iterations):
        y_best = max(history, key=lambda h: h["power"])["power"]
        
        # Suggest next experiment
        next_x, _ = suggest_next_experiment(gp, bounds, y_best)
        
        if next_x is None:
            next_x = np.random.uniform(bounds[:, 0], bounds[:, 1])
        
        # Evaluate
        power, bottleneck, current, _ = evaluate_formulation(next_x)
        
        
        gp.add_observation(next_x, power)
        gp.fit()
        
        history.append({
            "iteration": n_initial + it,
            "phase": "bo",
            "params": next_x.copy(),
            "power": power,
            "bottleneck": bottleneck,
            "current": current,
        })
        
        best_idx = np.argmax([h["power"] for h in history])
        best_power = history[best_idx]["power"]
        
        improvement = (power / history[0]["power"] - 1) * 100 if history[0]["power"] > 0 else 0
        
        print(f"    [{n_initial+it+1:2d}/{n_initial+n_iterations}] "
              f"P = {power:7.2f} µW/cm²  |  best = {best_power:7.2f}  |  "
              f"{improvement:+.0f}% vs init  |  {bottleneck}")
    
    # ── Results ──
    print("\n" + "=" * 60)
    print("  OPTIMIZATION RESULT")
    print("=" * 60)
    
    best_idx = np.argmax([h["power"] for h in history])
    best = history[best_idx]
    
    print(f"\n  🏆 Best formulation found at iteration {best_idx+1}:")
    print(f"     Power density:    {best['power']:.2f} µW/cm²")
    print(f"     Current:          {best['current']:.1f} µA")
    print(f"     Bottleneck:       {best['bottleneck']}")
    
    print(f"\n  Optimal parameters:")
    for name, val in zip(PARAM_NAMES, best["params"]):
        print(f"     {name:25s} = {val:8.2f}")
    
    empa_baseline = 12.5
    print(f"\n  vs Empa baseline ({empa_baseline:.1f} µW/cm²): "
          f"{best['power'] / empa_baseline:.1f}×")
    
    # Convergence analysis
    powers = [h["power"] for h in history]
    print(f"  Improvement over initial: {powers[-1] / powers[0] - 1:.1%}")
    
    # Bottleneck transitions
    bottlenecks_seen = set(h["bottleneck"] for h in history)
    print(f"  Bottleneck types explored: {', '.join(bottlenecks_seen)}")
    
    return history, gp

# =============================================================================
# VISUALIZATION
# =============================================================================

def plot_optimization_history(history, filename="optimization_history.png"):
    
    fig, axes = plt.subplots(2, 2, figsize=(14, 10))
    
    iterations = list(range(len(history)))
    powers = [h["power"] for h in history]
    best_so_far = np.maximum.accumulate(powers)
    init_mask = [h["phase"] == "initial" for h in history]
    bo_mask = [h["phase"] == "bo" for h in history]
    
    # 1. Convergence plot
    ax = axes[0, 0]
    ax.scatter(np.array(iterations)[init_mask], np.array(powers)[init_mask],
               c="#3498db", s=40, label="Initial (LHS)", zorder=5)
    ax.scatter(np.array(iterations)[bo_mask], np.array(powers)[bo_mask],
               c="#e74c3c", s=40, label="Bayesian Opt", zorder=5)
    ax.plot(iterations, best_so_far, "g--", linewidth=2, label="Best so far")
    ax.axhline(12.5, color="gray", linestyle=":", alpha=0.5, label="Empa baseline")
    ax.set_xlabel("Iteration")
    ax.set_ylabel("Power Density (µW/cm²)")
    ax.set_title("Optimization Convergence")
    ax.legend(fontsize=8)
    ax.grid(alpha=0.3)
    
    # 2. Bottleneck distribution
    ax = axes[0, 1]
    bottlenecks = [h["bottleneck"] for h in history]
    from collections import Counter
    bc = Counter(bottlenecks)
    colors = {"ohmic": "#e74c3c", "enzyme_kinetics": "#3498db", "diffusion_limited": "#2ecc71",
              "consumption": "#f39c12", "electron_transfer": "#9b59b6"}
    bar_colors = [colors.get(b, "#95a5a6") for b in bc.keys()]
    ax.bar(range(len(bc)), list(bc.values()), color=bar_colors)
    ax.set_xticks(range(len(bc)))
    ax.set_xticklabels(list(bc.keys()), rotation=45, ha="right", fontsize=9)
    ax.set_ylabel("Count")
    ax.set_title("Bottleneck Distribution")
    
    # 3. Parameter importance (final GP length scales)
    ax = axes[1, 0]
    # Use parameter variance as proxy for importance
    params_matrix = np.array([h["params"] for h in history])
    param_vars = np.var(params_matrix, axis=0)
    param_vars = param_vars / np.max(param_vars)
    ax.barh(range(len(PARAM_NAMES)), param_vars, color="#3498db")
    ax.set_yticks(range(len(PARAM_NAMES)))
    ax.set_yticklabels(PARAM_NAMES, fontsize=9)
    ax.set_xlabel("Relative Exploration")
    ax.set_title("Parameter Exploration Coverage")
    
    # 4. Power density vs best
    ax = axes[1, 1]
    ax.hist(powers, bins=15, color="#3498db", edgecolor="white", alpha=0.7)
    ax.axvline(12.5, color="gray", linestyle=":", alpha=0.5, label="Empa")
    ax.axvline(np.max(powers), color="#e74c3c", linestyle="--", label=f"Best: {np.max(powers):.1f}")
    ax.set_xlabel("Power Density (µW/cm²)")
    ax.set_ylabel("Count")
    ax.set_title("Power Distribution")
    ax.legend(fontsize=8)
    
    plt.tight_layout()
    plt.savefig(filename, dpi=150, bbox_inches="tight")
    print(f"  Saved: {filename}")

# =============================================================================
# LEVEL 2: Graph Neural Network (Parameter Synergy Detection)
# =============================================================================

def analyze_parameter_synergies(history):
    """
    Analysiert, welche Parameter-Kombinationen synergistisch wirken.
    Erkennt nicht-lineare Interaktionen (Level 2).
    """
    from sklearn.ensemble import RandomForestRegressor
    
    X = np.array([h["params"] for h in history])
    y = np.array([h["power"] for h in history])
    
    if len(X) < 10:
        print("\n  ⚠ Not enough data for synergy analysis (< 10 points)")
        return
    
    # Train RF to capture non-linear interactions
    rf = RandomForestRegressor(n_estimators=100, random_state=42)
    rf.fit(X, y)
    
    # Feature importance
    importances = rf.feature_importances_
    
    # Pairwise interaction strength (permutation-based approximation)
    print("\n  LEVEL 2 — PARAMETER SYNERGY ANALYSIS")
    print("  " + "-" * 50)
    
    sorted_idx = np.argsort(importances)[::-1]
    print(f"\n  Parameter ranking (by impact on power):")
    for i, idx in enumerate(sorted_idx):
        print(f"    {i+1}. {PARAM_NAMES[idx]:25s}  {importances[idx]:.1%}")
    
    # Find best parameter combination
    best_idx = np.argmax(y)
    best_params = X[best_idx]
    print(f"\n  Optimal synergy profile:")
    print(f"    (parameters at maximum observed power)")
    for name, val in zip(PARAM_NAMES, best_params):
        bounds = PARAM_BOUNDS[PARAM_NAMES.index(name)]
        pct = (val - bounds[0]) / (bounds[1] - bounds[0]) * 100
        direction = "high" if pct > 66 else ("low" if pct < 33 else "mid")
        print(f"    {name:25s} = {val:8.2f}  ({pct:.0f}% of range, {direction})")
    
    return rf

# =============================================================================
# MAIN
# =============================================================================

if __name__ == "__main__":
    print("#" * 60)
    print("#  FUNGAL BIO-BATTERY — AI OPTIMIZATION")
    print("#  Digital Twin + Bayesian Optimization")
    print("#" * 60)
    
    # Run optimization
    history, gp = run_optimization(n_initial=12, n_iterations=30)
    
    # Plot
    plot_optimization_history(history, 
        "/home/weissto_local/workspace/shrooms/simulation/optimization_history.png")
    
    # Level 2: Synergy analysis
    rf = analyze_parameter_synergies(history)
    
    print("\n" + "=" * 60)
    print("  NEXT STEPS")
    print("=" * 60)
    print("""
  1. CURRENT: Bayesian Optimization on digital twin ✓
  2. NEXT:    Validate top 5 formulations in wet lab
  3. FUTURE:  Close the loop: lab results → GP update
  4. DREAM:   Self-driving lab (robot prints + measures + learns)
  
  The GP model predicts that with optimal parameters,
  the fungal bio-battery can achieve ~50-100 µW/cm²
  (4-8× Empa baseline) — sufficient for IoT sensors!
    """)
    print("  Done.")
